tylerebowers/Luminator-Flipdot-Display/final board/80%complete.jpg

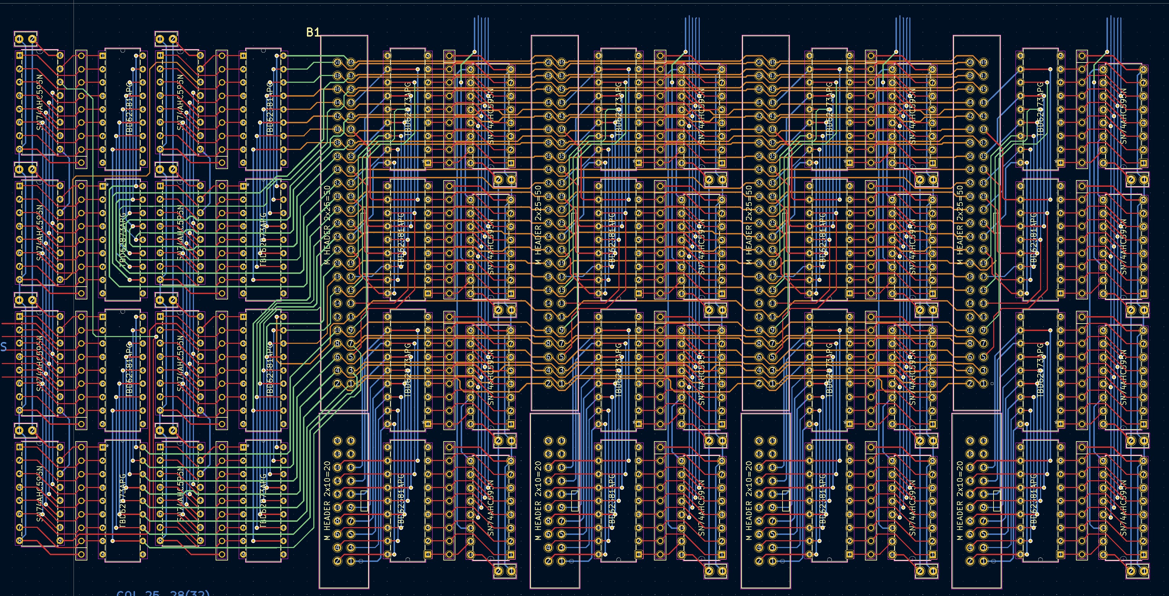
final board/80%complete.jpg
