tylerebowers/Luminator-Flipdot-Display/final board/90%complete.jpg

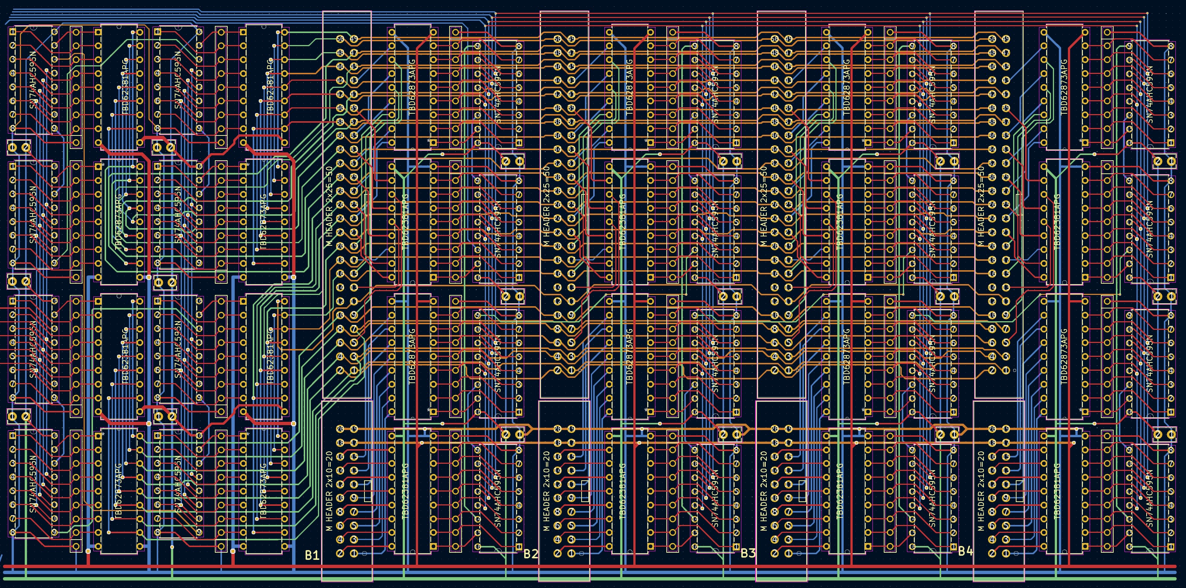
final board/90%complete.jpg
