tylerebowers/Luminator-Flipdot-Display/final board/100%Complete_3D.png

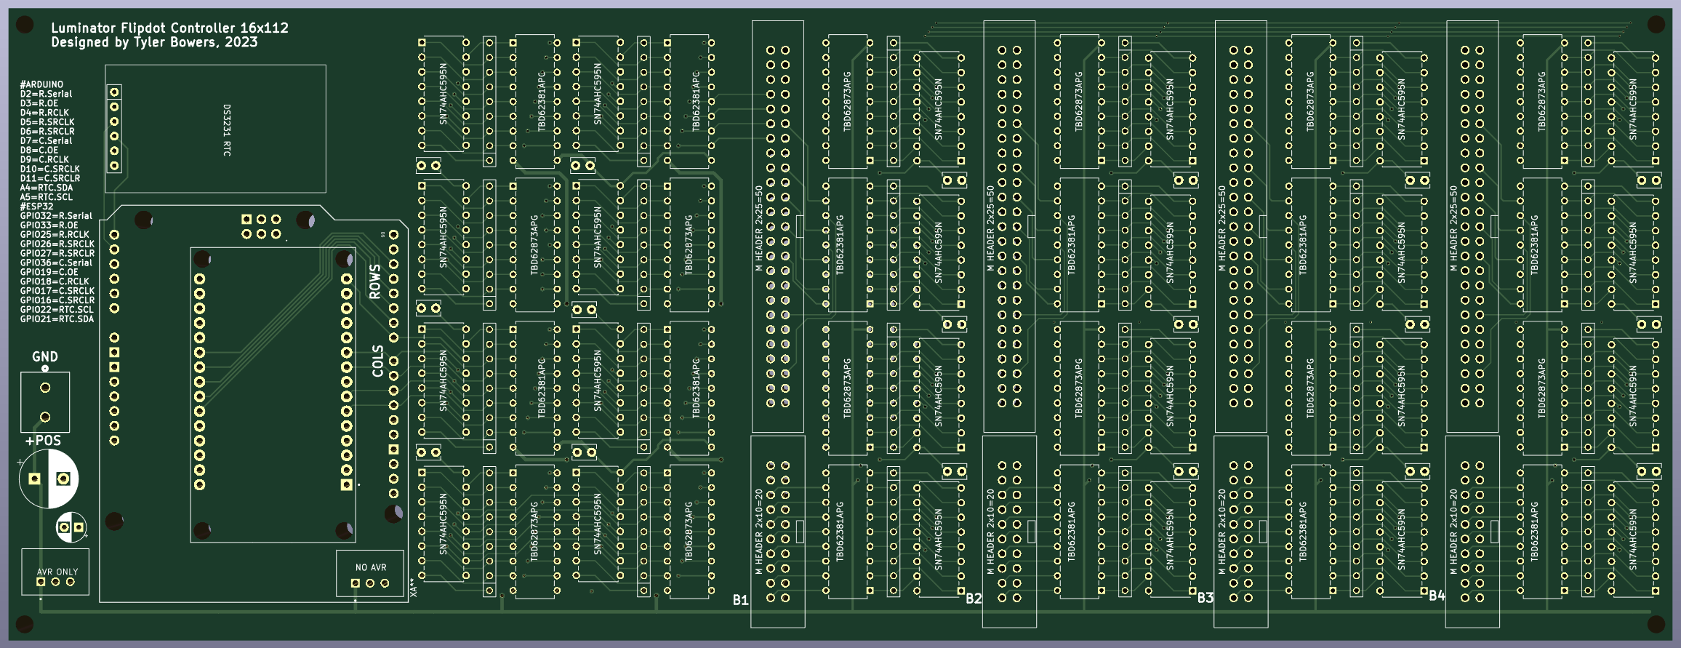
final board/100%Complete_3D.png
