tylerebowers/Luminator-Flipdot-Display/Other/board that doesn't work/Screenshot 2023-12-21 150835.png

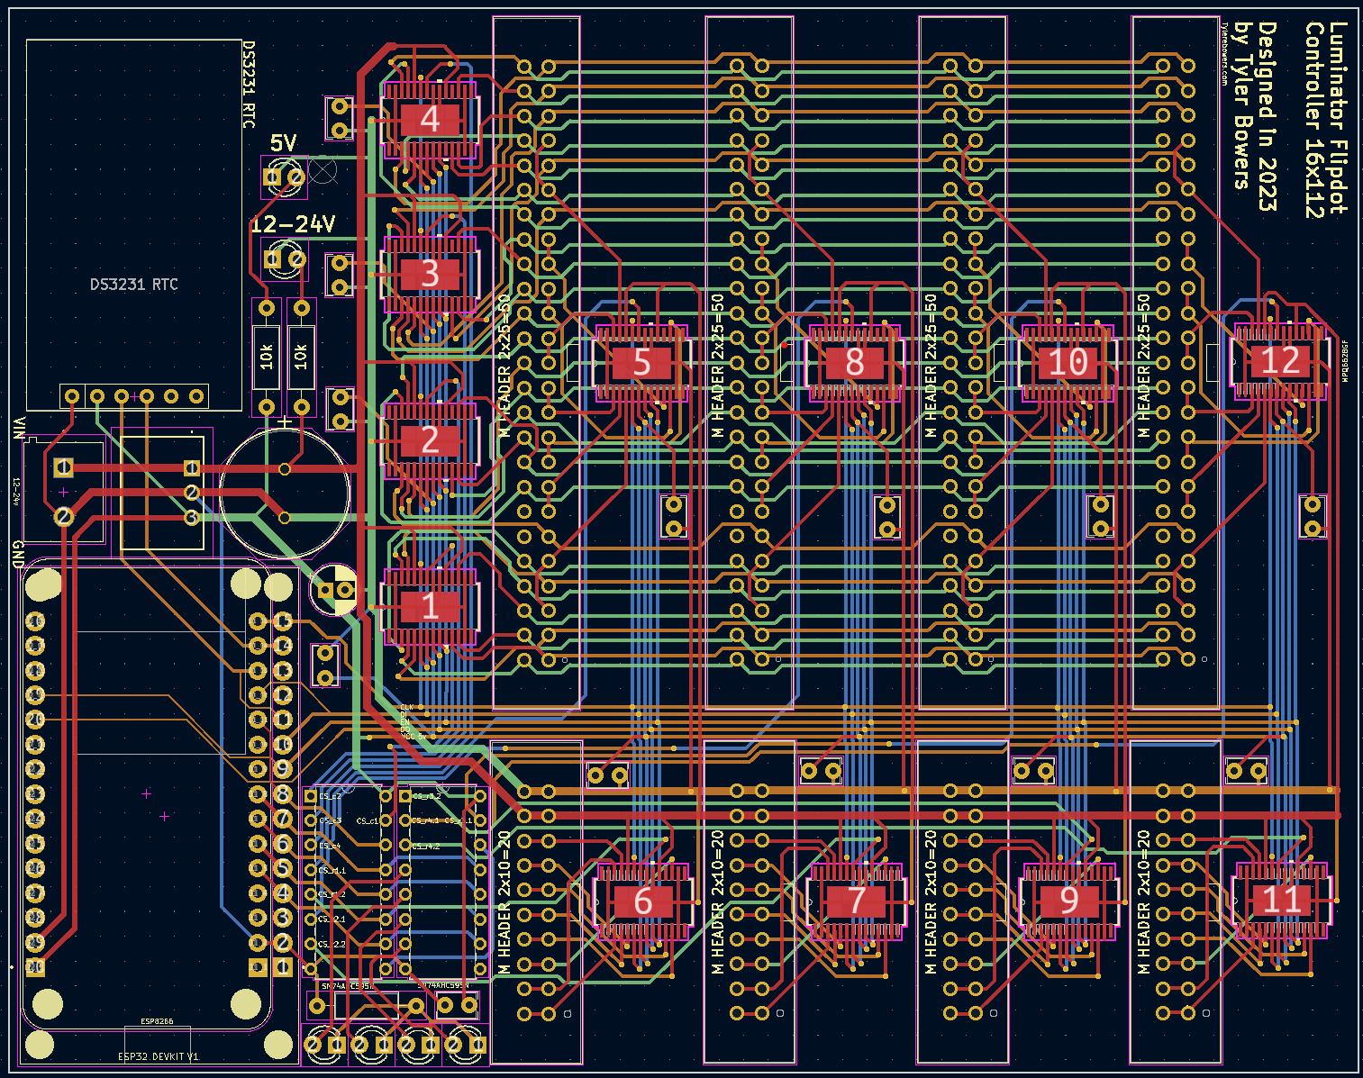
Other/board that doesn't work/Screenshot 2023-12-21 150835.png
