tylerebowers/Luminator-Flipdot-Display/Media/wiring.jpg

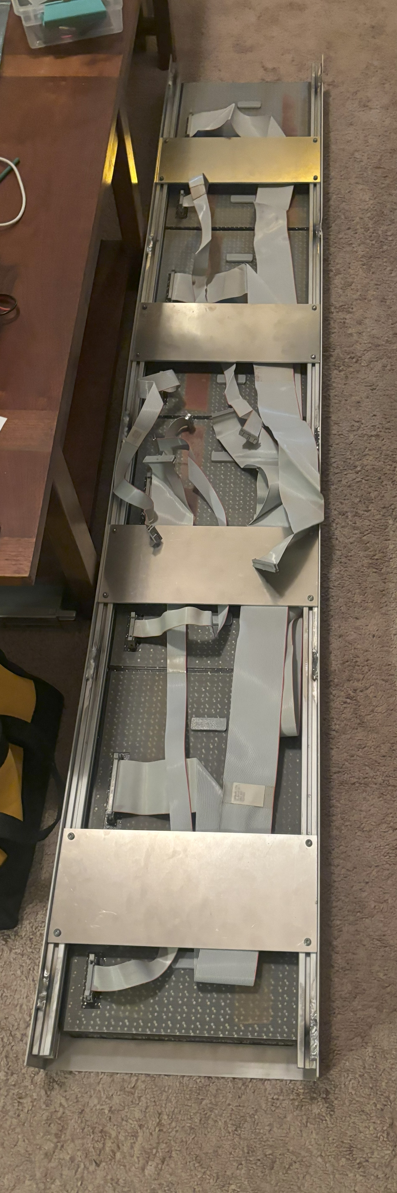
Media/wiring.jpg
