tylerebowers/Luminator-Flipdot-Display/Final Board/luminator.kicad_sch

## KiCad design Final Board/luminator.kicad_sch (2023-03-06)

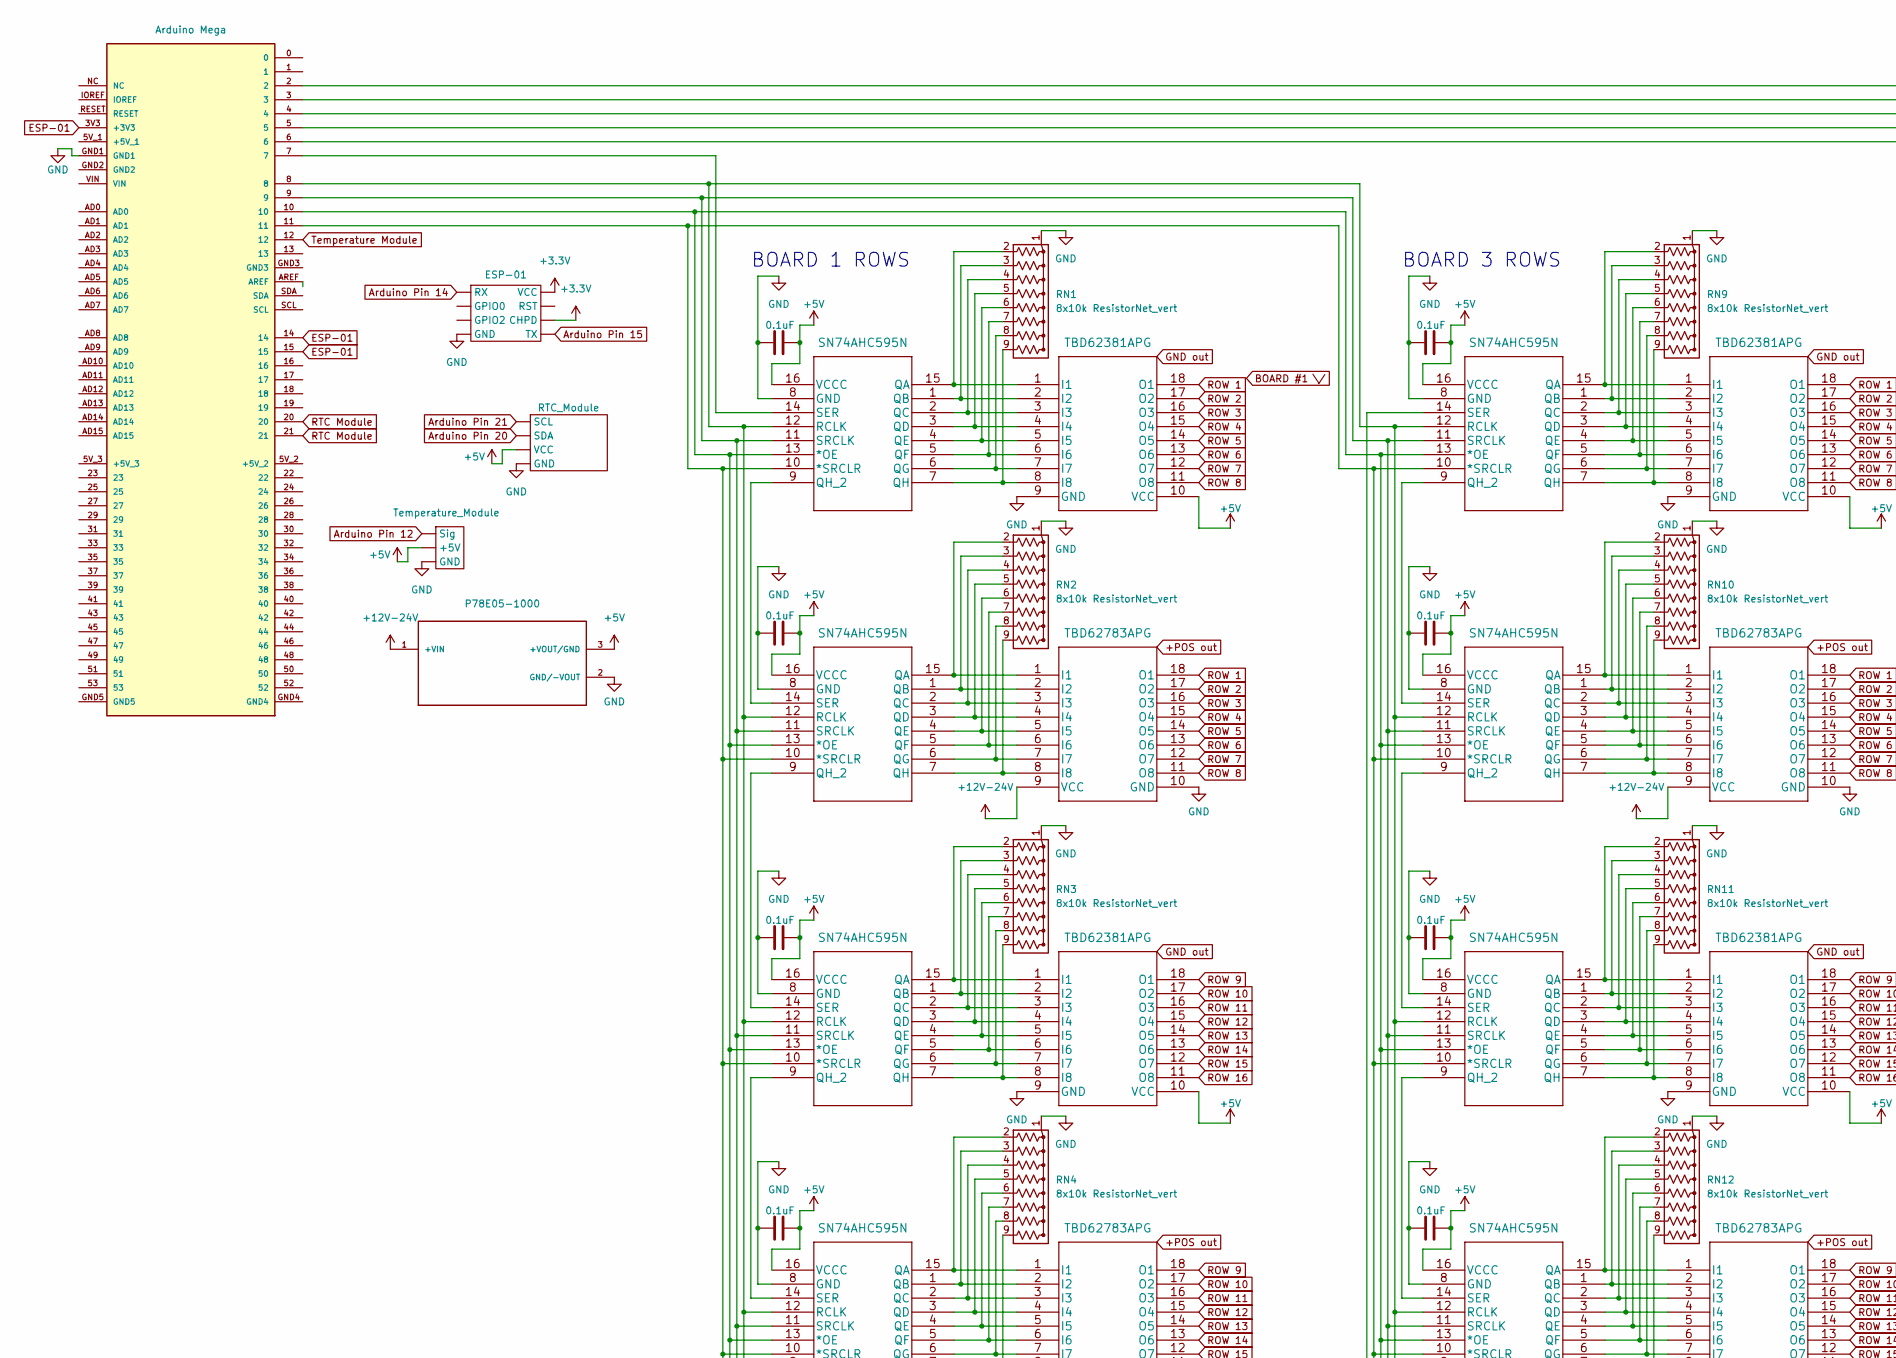
[picture p30: schematic luminator.kicad_sch, part in row 1, column 1]

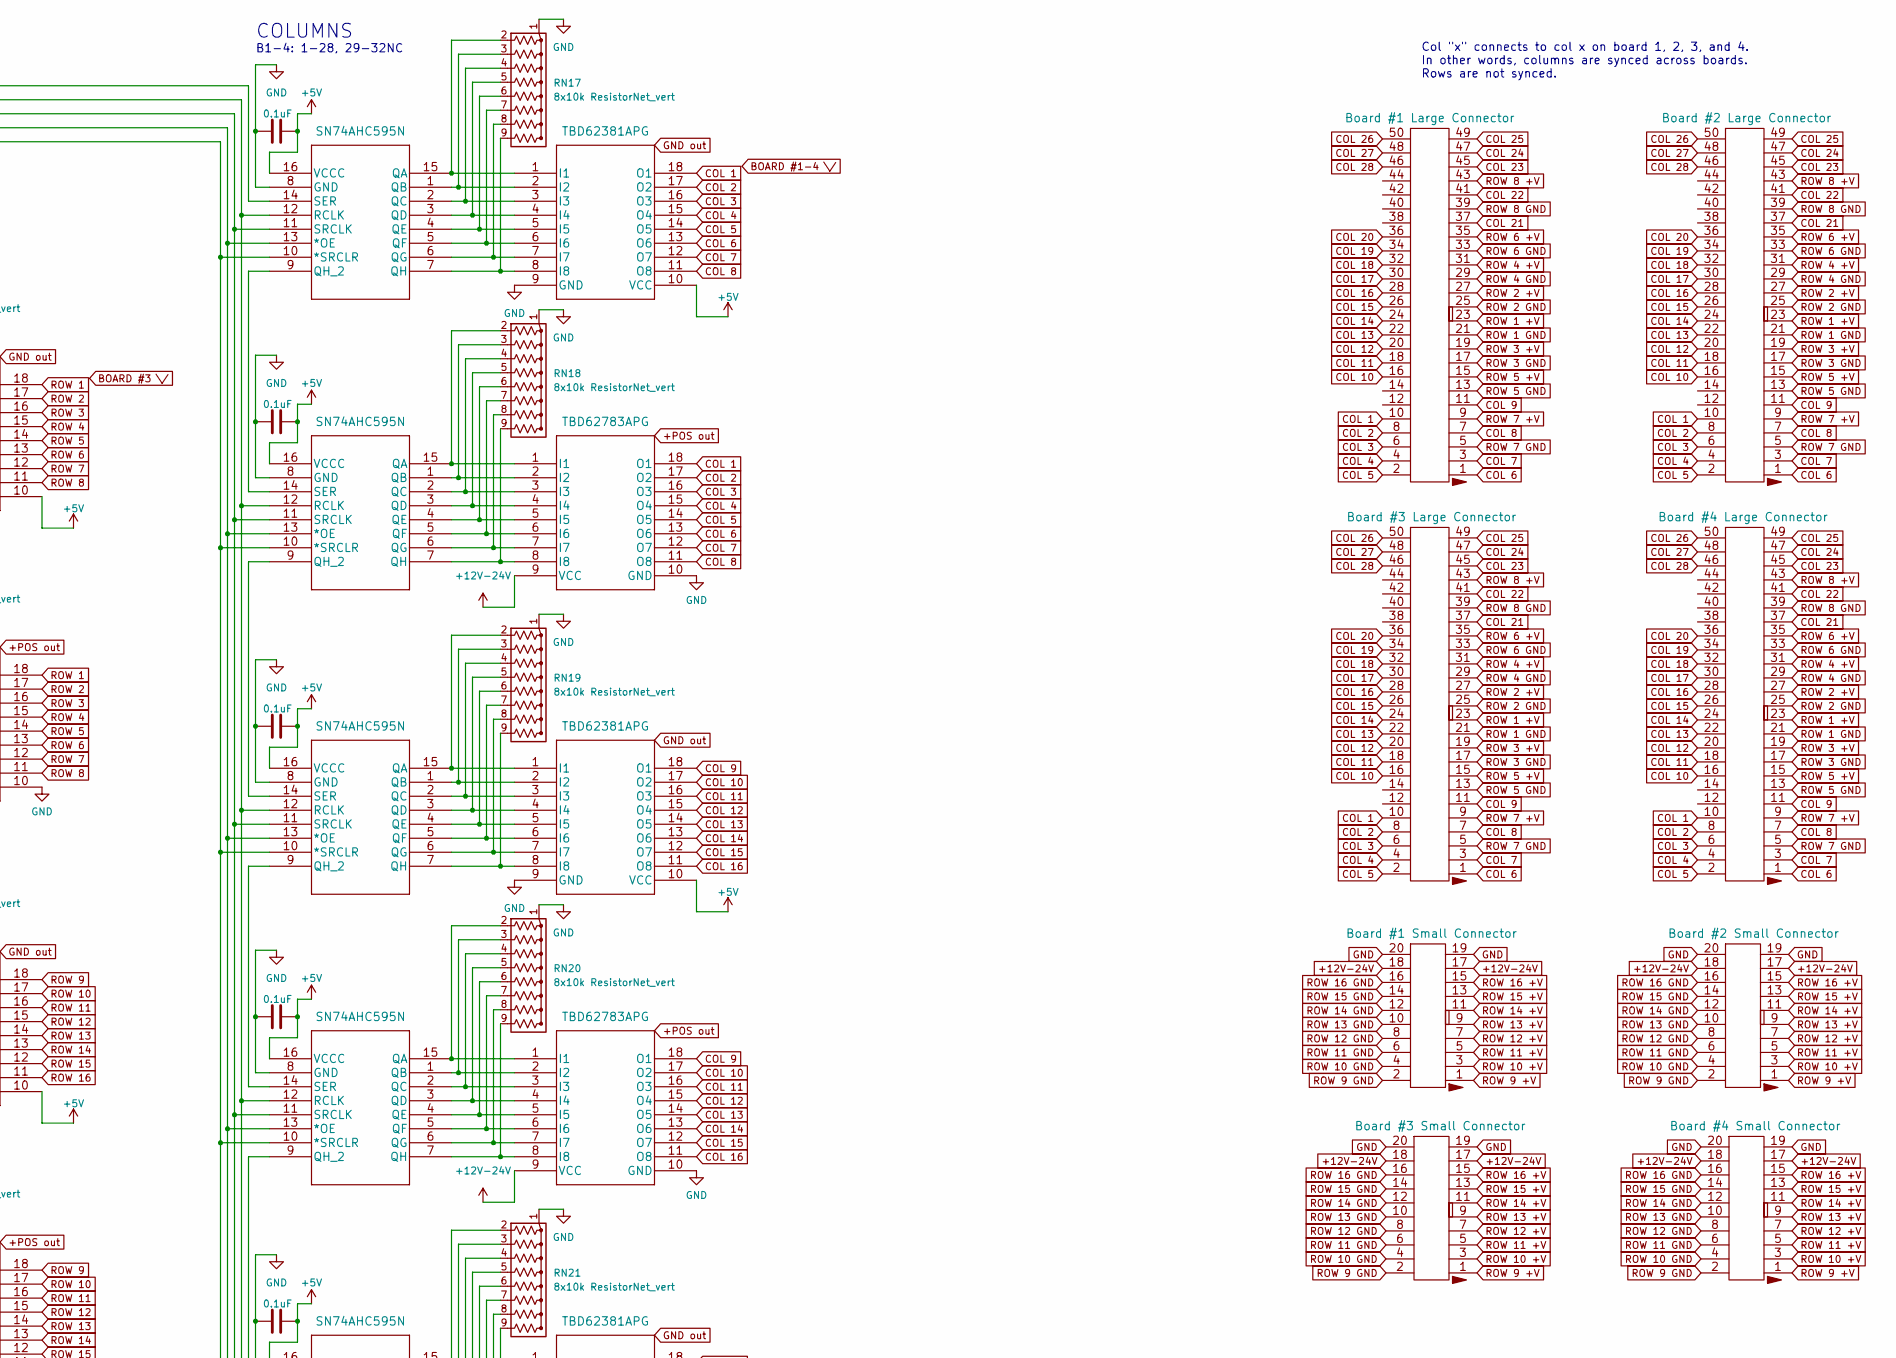
[picture p31: schematic luminator.kicad_sch, part in row 1, column 2]

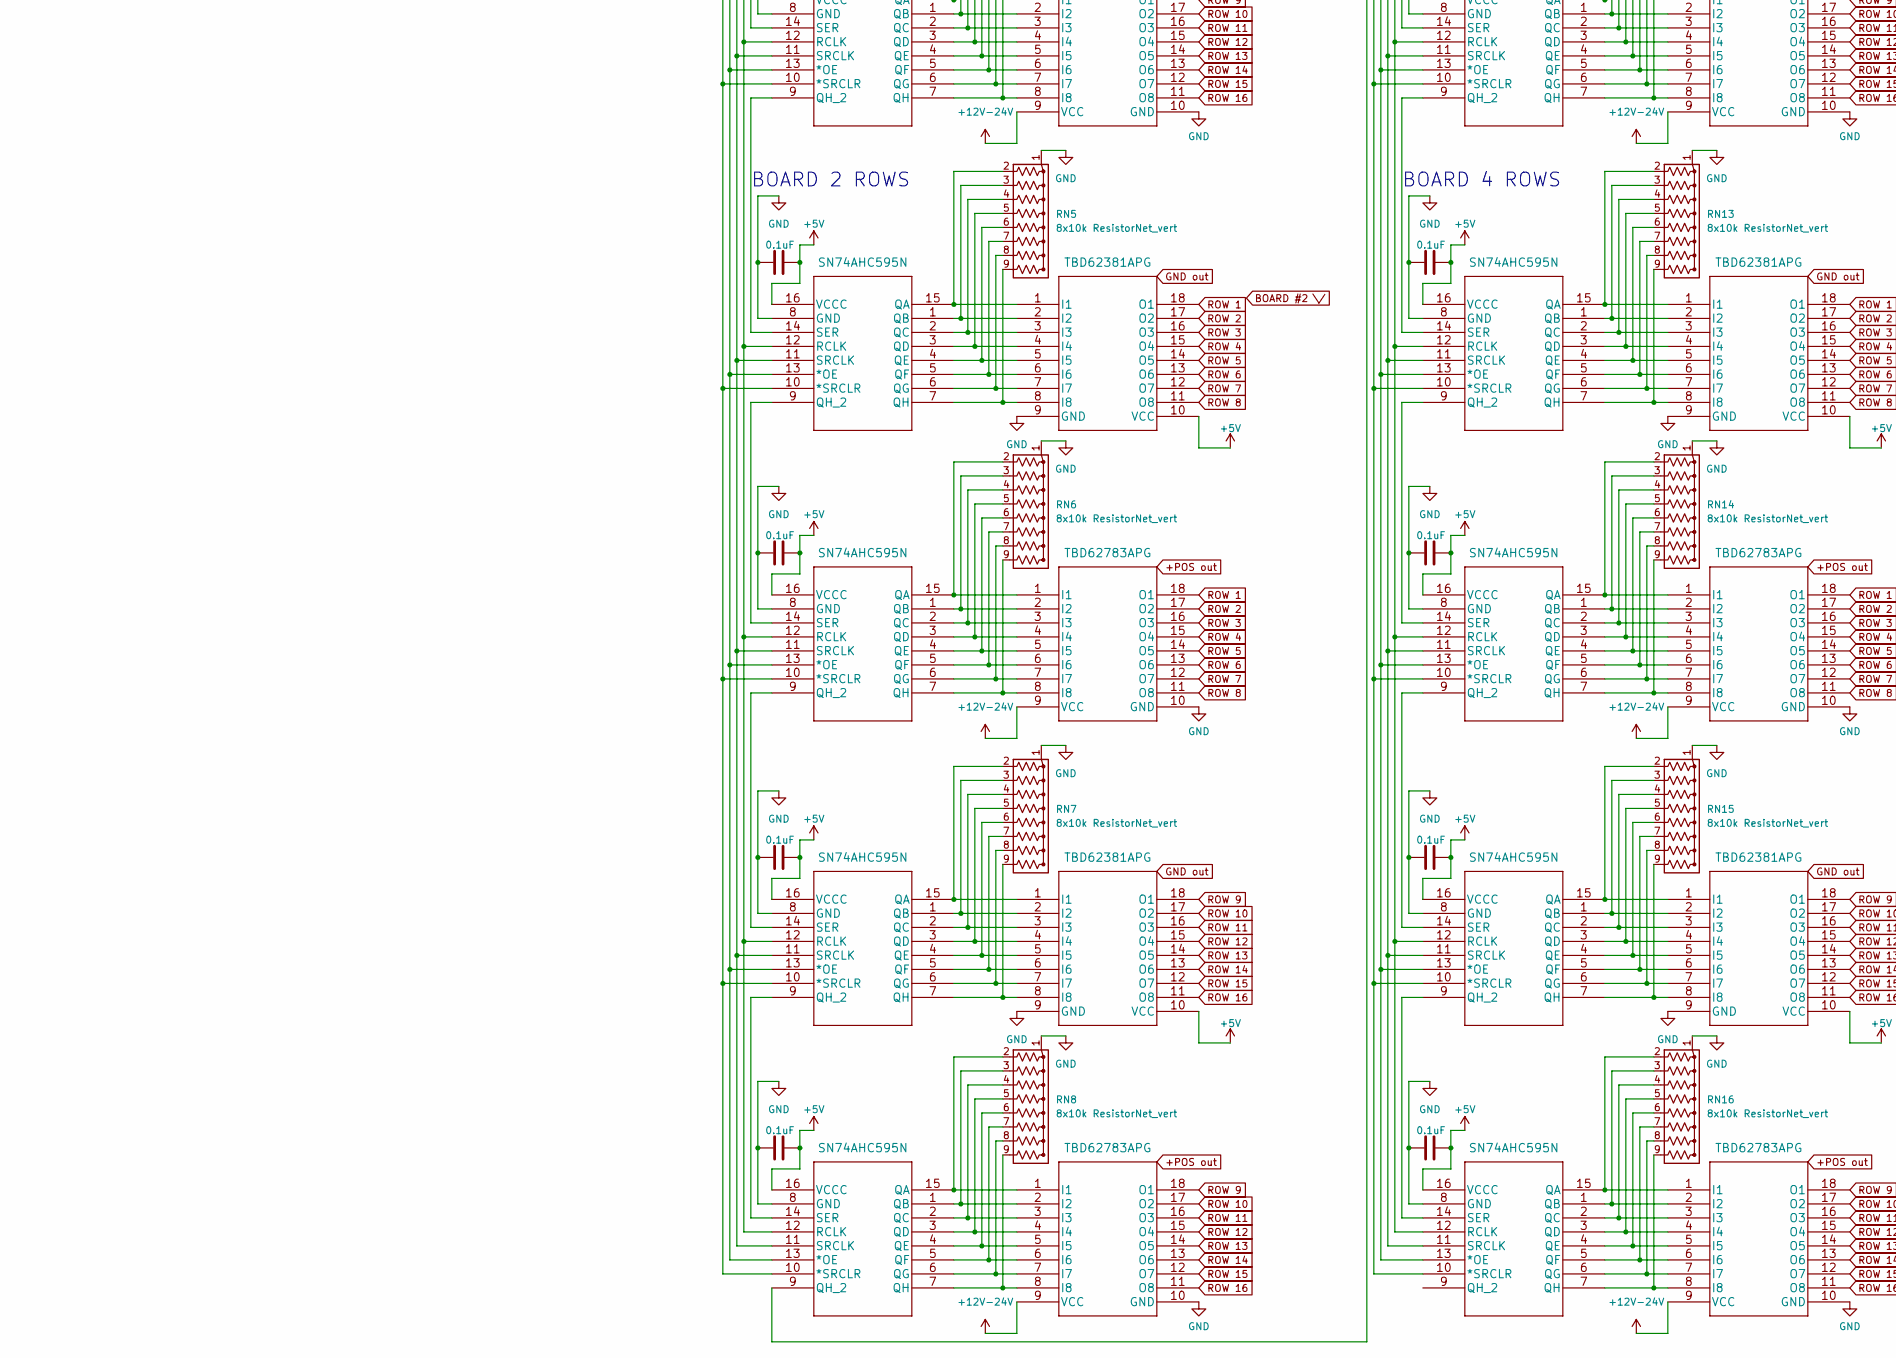
[picture p32: schematic luminator.kicad_sch, part in row 2, column 1]

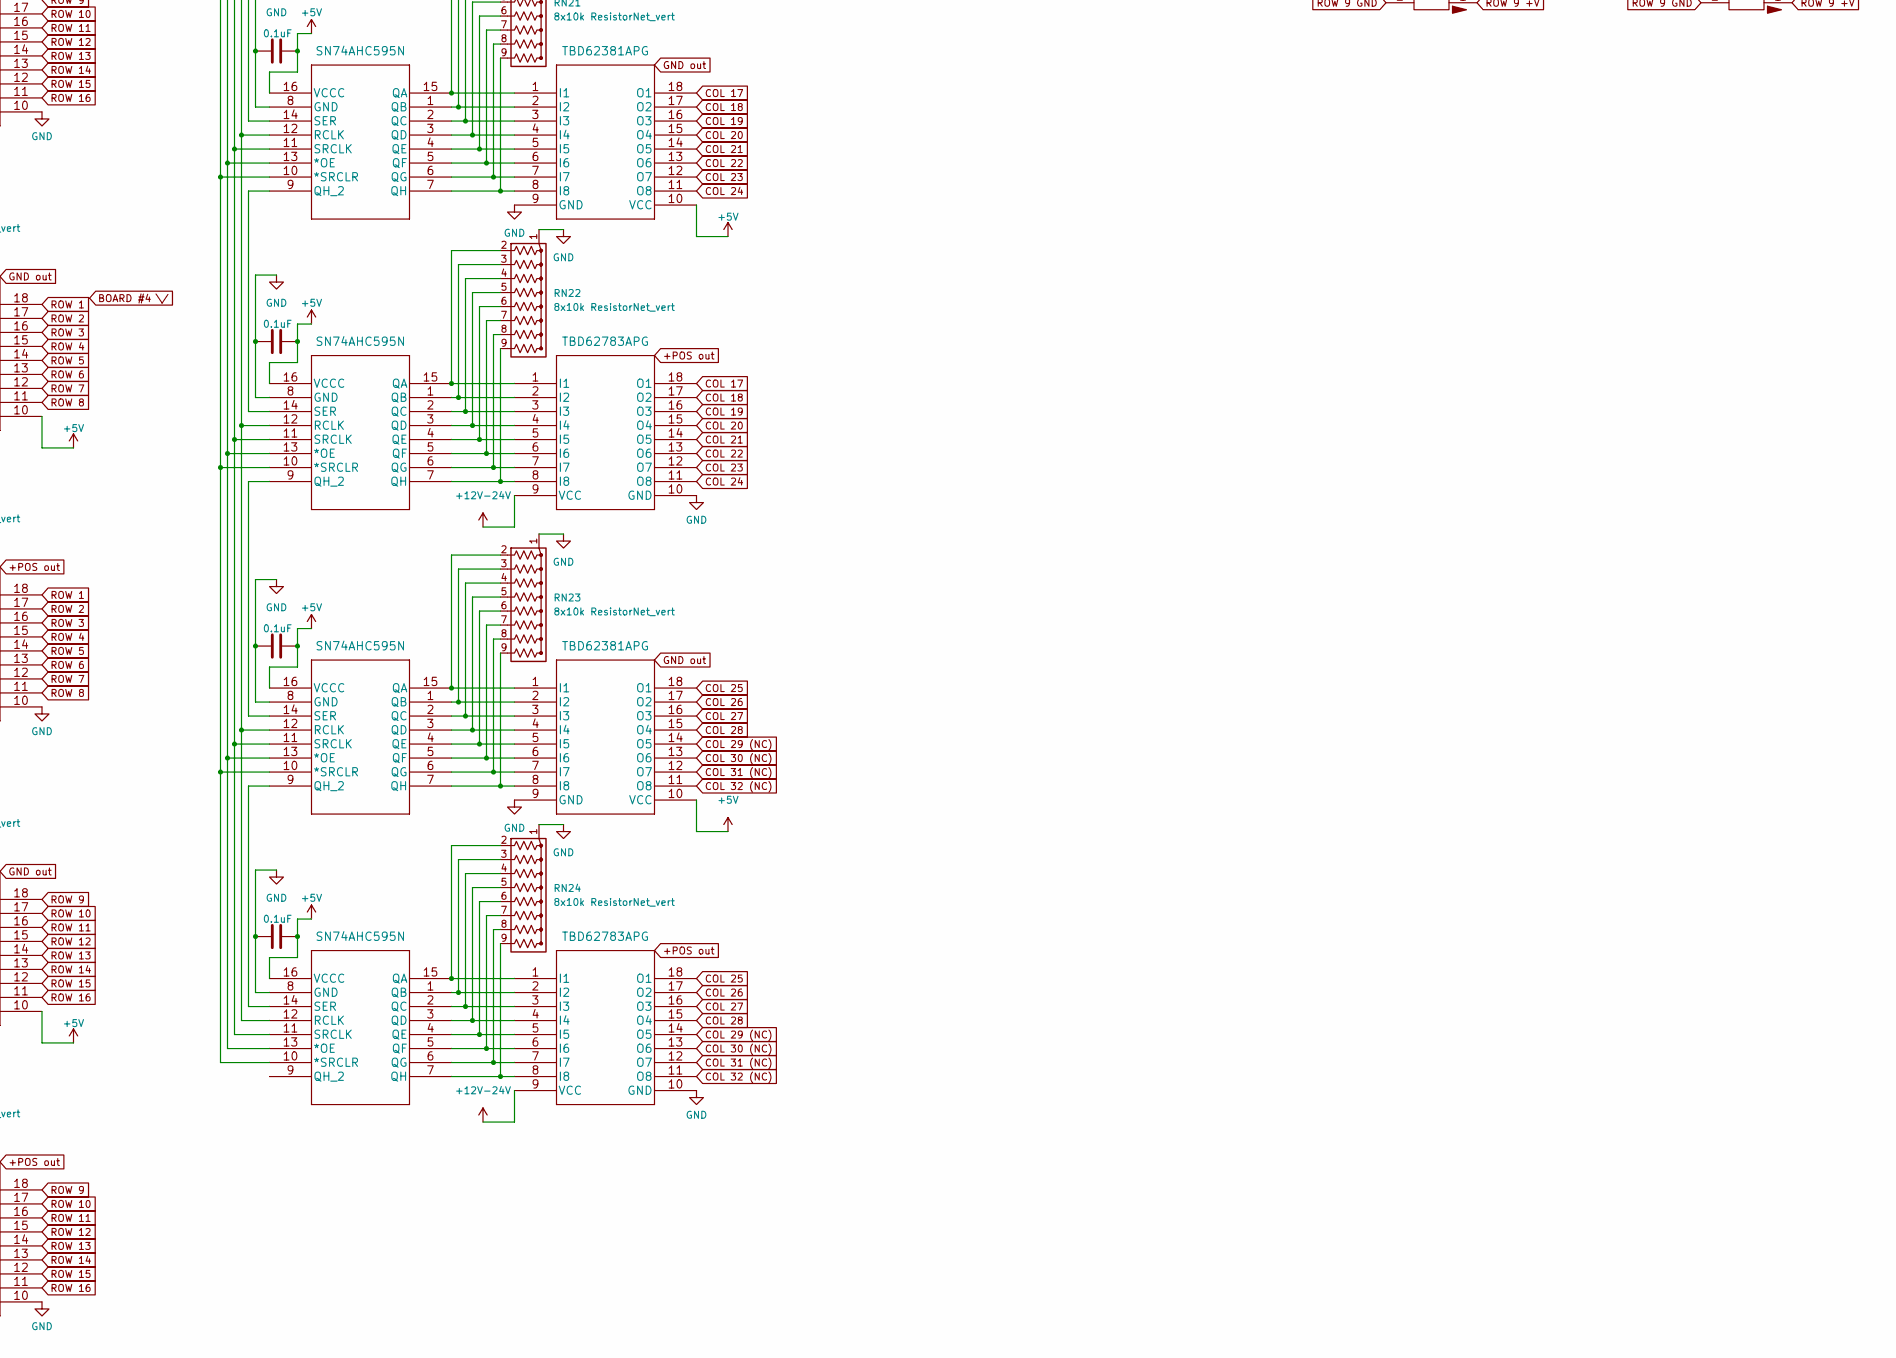
[picture p33: schematic luminator.kicad_sch, part in row 2, column 2]

Parts:
A1: Arduino Mega; ARDUINO_A000067
C1, C2, C3, C4, C5, C6, C7, C8, C9, C10, C11, C12, C13, C14, C15, C16, C17, C18, C19, C20, C21, C22, C23, C24: 0.1uF
J1: Board #1 Large Connector; CONN_SBH11-PBPC-D25-ST-BK_SUL
J2: Board #3 Large Connector; CONN_SBH11-PBPC-D25-ST-BK_SUL
J3: Board #1 Small Connector; CONN20_D10-ST-BK_SUL
J4: Board #3 Small Connector; CONN20_D10-ST-BK_SUL
J5: Board #2 Large Connector; CONN_SBH11-PBPC-D25-ST-BK_SUL
J6: Board #4 Large Connector; CONN_SBH11-PBPC-D25-ST-BK_SUL
J7: Board #2 Small Connector; CONN20_D10-ST-BK_SUL
J8: Board #4 Small Connector; CONN20_D10-ST-BK_SUL
PS1: P78E05-1000; CONV_P78E05-1000
RN1, RN2, RN3, RN4, RN5, RN6, RN7, RN8, RN9, RN10, RN11, RN12, RN13, RN14, RN15, RN16, RN17, RN18, RN19, RN20, RN21, RN22, RN23, RN24: 8x10k ResistorNet_vert; R_Array_SIP10
U1: Temperature_Module
U2: ESP-01
U3: RTC_Module
U4, U5, U6, U7, U8, U9, U10, U11, U20, U21, U22, U23, U24, U25, U26, U27, U36, U37, U38, U39, U40, U41, U42, U43: SN74AHC595N; N16
U12, U14, U16, U18, U28, U30, U32, U34, U44, U46, U48, U50: TBD62381APG; P-DIP18-300-2p54-001_TOS
U13, U15, U17, U19, U29, U31, U33, U35, U45, U47, U49, U51: TBD62783APG; P-DIP18-300-2p54-001_TOS

Connections:
+3.3V: U2.
+5V: C1.2, C2.2, C3.2, C4.2, C5.2, C6.2, C7.2, C8.2, C9.2, C10.2, C11.2, C12.2, C13.2, C14.2, C15.2, C16.2, C17.2, C18.2, C19.2, C20.2, C21.2, C22.2, C23.2, C24.2, PS1.3 (+VOUT/GND), U1., U3., U4.16 (VCCC), U5.16 (VCCC), U6.16 (VCCC), U7.16 (VCCC), U8.16 (VCCC), U9.16 (VCCC), U10.16 (VCCC), U11.16 (VCCC), U12.10 (VCC), U14.10 (VCC), U16.10 (VCC), U18.10 (VCC), U20.16 (VCCC), U21.16 (VCCC), U22.16 (VCCC), U23.16 (VCCC), U24.16 (VCCC), U25.16 (VCCC), U26.16 (VCCC), U27.16 (VCCC), U28.10 (VCC), U30.10 (VCC), U32.10 (VCC), U34.10 (VCC), U36.16 (VCCC), U37.16 (VCCC), U38.16 (VCCC), U39.16 (VCCC), U40.16 (VCCC), U41.16 (VCCC), U42.16 (VCCC), U43.16 (VCCC), U44.10 (VCC), U46.10 (VCC), U48.10 (VCC), U50.10 (VCC)
+12V-24V: J3.17, J3.18, J4.17, J4.18, J7.17, J7.18, J8.17, J8.18, PS1.1 (+VIN), U13.9 (VCC), U15.9 (VCC), U17.9 (VCC), U19.9 (VCC), U29.9 (VCC), U31.9 (VCC), U33.9 (VCC), U35.9 (VCC), U45.9 (VCC), U47.9 (VCC), U49.9 (VCC), U51.9 (VCC)
Arduino Pin 12: U1.
Arduino Pin 14: U2.
Arduino Pin 15: U2.
Arduino Pin 20: U3.
Arduino Pin 21: U3.
COL 1: J1.10, J2.10, J5.10, J6.10, U44.18 (O1), U45.18 (O1)
COL 2: J1.8, J2.8, J5.8, J6.8, U44.17 (O2), U45.17 (O2)
COL 3: J1.6, J2.6, J5.6, J6.6, U44.16 (O3), U45.16 (O3)
COL 4: J1.4, J2.4, J5.4, J6.4, U44.15 (O4), U45.15 (O4)
COL 5: J1.2, J2.2, J5.2, J6.2, U44.14 (O5), U45.14 (O5)
COL 6: J1.1, J2.1, J5.1, J6.1, U44.13 (O6), U45.13 (O6)
COL 7: J1.3, J2.3, J5.3, J6.3, U44.12 (O7), U45.12 (O7)
COL 8: J1.7, J2.7, J5.7, J6.7, U44.11 (O8), U45.11 (O8)
COL 9: J1.11, J2.11, J5.11, J6.11, U46.18 (O1), U47.18 (O1)
COL 10: J1.16, J2.16, J5.16, J6.16, U46.17 (O2), U47.17 (O2)
COL 11: J1.18, J2.18, J5.18, J6.18, U46.16 (O3), U47.16 (O3)
COL 12: J1.20, J2.20, J5.20, J6.20, U46.15 (O4), U47.15 (O4)
COL 13: J1.22, J2.22, J5.22, J6.22, U46.14 (O5), U47.14 (O5)
COL 14: J1.24, J2.24, J5.24, J6.24, U46.13 (O6), U47.13 (O6)
COL 15: J1.26, J2.26, J5.26, J6.26, U46.12 (O7), U47.12 (O7)
COL 16: J1.28, J2.28, J5.28, J6.28, U46.11 (O8), U47.11 (O8)
COL 17: J1.30, J2.30, J5.30, J6.30, U48.18 (O1), U49.18 (O1)
COL 18: J1.32, J2.32, J5.32, J6.32, U48.17 (O2), U49.17 (O2)
COL 19: J1.34, J2.34, J5.34, J6.34, U48.16 (O3), U49.16 (O3)
COL 20: J1.36, J2.36, J5.36, J6.36, U48.15 (O4), U49.15 (O4)
COL 21: J1.37, J2.37, J5.37, J6.37, U48.14 (O5), U49.14 (O5)
COL 22: J1.41, J2.41, J5.41, J6.41, U48.13 (O6), U49.13 (O6)
COL 23: J1.45, J2.45, J5.45, J6.45, U48.12 (O7), U49.12 (O7)
COL 24: J1.47, J2.47, J5.47, J6.47, U48.11 (O8), U49.11 (O8)
COL 25: J1.49, J2.49, J5.49, J6.49, U50.18 (O1), U51.18 (O1)
COL 26: J1.50, J2.50, J5.50, J6.50, U50.17 (O2), U51.17 (O2)
COL 27: J1.48, J2.48, J5.48, J6.48, U50.16 (O3), U51.16 (O3)
COL 28: J1.46, J2.46, J5.46, J6.46, U50.15 (O4), U51.15 (O4)
COL 29 (NC): U50.14 (O5), U51.14 (O5)
COL 30 (NC): U50.13 (O6), U51.13 (O6)
COL 31 (NC): U50.12 (O7), U51.12 (O7)
COL 32 (NC): U50.11 (O8), U51.11 (O8)
ESP-01: A1.3V3 (+3V3), A1.14, A1.15
GND: A1.GND1, C1.1, C2.1, C3.1, C4.1, C5.1, C6.1, C7.1, C8.1, C9.1, C10.1, C11.1, C12.1, C13.1, C14.1, C15.1, C16.1, C17.1, C18.1, C19.1, C20.1, C21.1, C22.1, C23.1, C24.1, J3.19, J3.20, J4.19, J4.20, J7.19, J7.20, J8.19, J8.20, PS1.2 (GND/-VOUT), RN1.1 (common), RN2.1 (common), RN3.1 (common), RN4.1 (common), RN5.1 (common), RN6.1 (common), RN7.1 (common), RN8.1 (common), RN9.1 (common), RN10.1 (common), RN11.1 (common), RN12.1 (common), RN13.1 (common), RN14.1 (common), RN15.1 (common), RN16.1 (common), RN17.1 (common), RN18.1 (common), RN19.1 (common), RN20.1 (common), RN21.1 (common), RN22.1 (common), RN23.1 (common), RN24.1 (common), U1., U2., U3., U4.8 (GND), U5.8 (GND), U6.8 (GND), U7.8 (GND), U8.8 (GND), U9.8 (GND), U10.8 (GND), U11.8 (GND), U12.9 (GND), U13.10 (GND), U14.9 (GND), U15.10 (GND), U16.9 (GND), U17.10 (GND), U18.9 (GND), U19.10 (GND), U20.8 (GND), U21.8 (GND), U22.8 (GND), U23.8 (GND), U24.8 (GND), U25.8 (GND), U26.8 (GND), U27.8 (GND), U28.9 (GND), U29.10 (GND), U30.9 (GND), U31.10 (GND), U32.9 (GND), U33.10 (GND), U34.9 (GND), U35.10 (GND), U36.8 (GND), U37.8 (GND), U38.8 (GND), U39.8 (GND), U40.8 (GND), U41.8 (GND), U42.8 (GND), U43.8 (GND), U44.9 (GND), U45.10 (GND), U46.9 (GND), U47.10 (GND), U48.9 (GND), U49.10 (GND), U50.9 (GND), U51.10 (GND)
unnamed: A1.2, U36.14 (SER)
unnamed: A1.3, U36.12 (RCLK), U37.12 (RCLK), U38.12 (RCLK), U39.12 (RCLK), U40.12 (RCLK), U41.12 (RCLK), U42.12 (RCLK), U43.12 (RCLK)
unnamed: A1.4, U36.11 (SRCLK), U37.11 (SRCLK), U38.11 (SRCLK), U39.11 (SRCLK), U40.11 (SRCLK), U41.11 (SRCLK), U42.11 (SRCLK), U43.11 (SRCLK)
unnamed: A1.5, U36.13 (*OE), U37.13 (*OE), U38.13 (*OE), U39.13 (*OE), U40.13 (*OE), U41.13 (*OE), U42.13 (*OE), U43.13 (*OE)
unnamed: A1.6, U36.10 (*SRCLR), U37.10 (*SRCLR), U38.10 (*SRCLR), U39.10 (*SRCLR), U40.10 (*SRCLR), U41.10 (*SRCLR), U42.10 (*SRCLR), U43.10 (*SRCLR)
unnamed: A1.7, U4.14 (SER)
unnamed: A1.8, U4.12 (RCLK), U5.12 (RCLK), U6.12 (RCLK), U7.12 (RCLK), U8.12 (RCLK), U9.12 (RCLK), U10.12 (RCLK), U11.12 (RCLK), U20.12 (RCLK), U21.12 (RCLK), U22.12 (RCLK), U23.12 (RCLK), U24.12 (RCLK), U25.12 (RCLK), U26.12 (RCLK), U27.12 (RCLK)
unnamed: A1.9, U4.11 (SRCLK), U5.11 (SRCLK), U6.11 (SRCLK), U7.11 (SRCLK), U8.11 (SRCLK), U9.11 (SRCLK), U10.11 (SRCLK), U11.11 (SRCLK), U20.11 (SRCLK), U21.11 (SRCLK), U22.11 (SRCLK), U23.11 (SRCLK), U24.11 (SRCLK), U25.11 (SRCLK), U26.11 (SRCLK), U27.11 (SRCLK)
unnamed: A1.10, U4.13 (*OE), U5.13 (*OE), U6.13 (*OE), U7.13 (*OE), U8.13 (*OE), U9.13 (*OE), U10.13 (*OE), U11.13 (*OE), U20.13 (*OE), U21.13 (*OE), U22.13 (*OE), U23.13 (*OE), U24.13 (*OE), U25.13 (*OE), U26.13 (*OE), U27.13 (*OE)
unnamed: A1.11, U4.10 (*SRCLR), U5.10 (*SRCLR), U6.10 (*SRCLR), U7.10 (*SRCLR), U8.10 (*SRCLR), U9.10 (*SRCLR), U10.10 (*SRCLR), U11.10 (*SRCLR), U20.10 (*SRCLR), U21.10 (*SRCLR), U22.10 (*SRCLR), U23.10 (*SRCLR), U24.10 (*SRCLR), U25.10 (*SRCLR), U26.10 (*SRCLR), U27.10 (*SRCLR)
unnamed: RN1.2 (R1), U4.15 (QA), U12.1 (I1)
unnamed: RN1.3 (R2), U4.1 (QB), U12.2 (I2)
unnamed: RN1.4 (R3), U4.2 (QC), U12.3 (I3)
unnamed: RN1.5 (R4), U4.3 (QD), U12.4 (I4)
unnamed: RN1.6 (R5), U4.4 (QE), U12.5 (I5)
unnamed: RN1.7 (R6), U4.5 (QF), U12.6 (I6)
unnamed: RN1.8 (R7), U4.6 (QG), U12.7 (I7)
unnamed: RN1.9 (R8), U4.7 (QH), U12.8 (I8)
unnamed: RN2.2 (R1), U5.15 (QA), U13.1 (I1)
unnamed: RN2.3 (R2), U5.1 (QB), U13.2 (I2)
unnamed: RN2.4 (R3), U5.2 (QC), U13.3 (I3)
unnamed: RN2.5 (R4), U5.3 (QD), U13.4 (I4)
unnamed: RN2.6 (R5), U5.4 (QE), U13.5 (I5)
unnamed: RN2.7 (R6), U5.5 (QF), U13.6 (I6)
unnamed: RN2.8 (R7), U5.6 (QG), U13.7 (I7)
unnamed: RN2.9 (R8), U5.7 (QH), U13.8 (I8)
unnamed: RN3.2 (R1), U6.15 (QA), U14.1 (I1)
unnamed: RN3.3 (R2), U6.1 (QB), U14.2 (I2)
unnamed: RN3.4 (R3), U6.2 (QC), U14.3 (I3)
unnamed: RN3.5 (R4), U6.3 (QD), U14.4 (I4)
unnamed: RN3.6 (R5), U6.4 (QE), U14.5 (I5)
unnamed: RN3.7 (R6), U6.5 (QF), U14.6 (I6)
unnamed: RN3.8 (R7), U6.6 (QG), U14.7 (I7)
unnamed: RN3.9 (R8), U6.7 (QH), U14.8 (I8)
unnamed: RN4.2 (R1), U7.15 (QA), U15.1 (I1)
unnamed: RN4.3 (R2), U7.1 (QB), U15.2 (I2)
unnamed: RN4.4 (R3), U7.2 (QC), U15.3 (I3)
unnamed: RN4.5 (R4), U7.3 (QD), U15.4 (I4)
unnamed: RN4.6 (R5), U7.4 (QE), U15.5 (I5)
unnamed: RN4.7 (R6), U7.5 (QF), U15.6 (I6)
unnamed: RN4.8 (R7), U7.6 (QG), U15.7 (I7)
unnamed: RN4.9 (R8), U7.7 (QH), U15.8 (I8)
unnamed: RN5.2 (R1), U8.15 (QA), U16.1 (I1)
unnamed: RN5.3 (R2), U8.1 (QB), U16.2 (I2)
unnamed: RN5.4 (R3), U8.2 (QC), U16.3 (I3)
unnamed: RN5.5 (R4), U8.3 (QD), U16.4 (I4)
unnamed: RN5.6 (R5), U8.4 (QE), U16.5 (I5)
unnamed: RN5.7 (R6), U8.5 (QF), U16.6 (I6)
unnamed: RN5.8 (R7), U8.6 (QG), U16.7 (I7)
unnamed: RN5.9 (R8), U8.7 (QH), U16.8 (I8)
unnamed: RN6.2 (R1), U9.15 (QA), U17.1 (I1)
unnamed: RN6.3 (R2), U9.1 (QB), U17.2 (I2)
unnamed: RN6.4 (R3), U9.2 (QC), U17.3 (I3)
unnamed: RN6.5 (R4), U9.3 (QD), U17.4 (I4)
unnamed: RN6.6 (R5), U9.4 (QE), U17.5 (I5)
unnamed: RN6.7 (R6), U9.5 (QF), U17.6 (I6)
unnamed: RN6.8 (R7), U9.6 (QG), U17.7 (I7)
unnamed: RN6.9 (R8), U9.7 (QH), U17.8 (I8)
unnamed: RN7.2 (R1), U10.15 (QA), U18.1 (I1)
unnamed: RN7.3 (R2), U10.1 (QB), U18.2 (I2)
unnamed: RN7.4 (R3), U10.2 (QC), U18.3 (I3)
unnamed: RN7.5 (R4), U10.3 (QD), U18.4 (I4)
unnamed: RN7.6 (R5), U10.4 (QE), U18.5 (I5)
unnamed: RN7.7 (R6), U10.5 (QF), U18.6 (I6)
unnamed: RN7.8 (R7), U10.6 (QG), U18.7 (I7)
unnamed: RN7.9 (R8), U10.7 (QH), U18.8 (I8)
unnamed: RN8.2 (R1), U11.15 (QA), U19.1 (I1)
unnamed: RN8.3 (R2), U11.1 (QB), U19.2 (I2)
unnamed: RN8.4 (R3), U11.2 (QC), U19.3 (I3)
unnamed: RN8.5 (R4), U11.3 (QD), U19.4 (I4)
unnamed: RN8.6 (R5), U11.4 (QE), U19.5 (I5)
unnamed: RN8.7 (R6), U11.5 (QF), U19.6 (I6)
unnamed: RN8.8 (R7), U11.6 (QG), U19.7 (I7)
unnamed: RN8.9 (R8), U11.7 (QH), U19.8 (I8)
unnamed: RN9.2 (R1), U20.15 (QA), U28.1 (I1)
unnamed: RN9.3 (R2), U20.1 (QB), U28.2 (I2)
unnamed: RN9.4 (R3), U20.2 (QC), U28.3 (I3)
unnamed: RN9.5 (R4), U20.3 (QD), U28.4 (I4)
unnamed: RN9.6 (R5), U20.4 (QE), U28.5 (I5)
unnamed: RN9.7 (R6), U20.5 (QF), U28.6 (I6)
unnamed: RN9.8 (R7), U20.6 (QG), U28.7 (I7)
unnamed: RN9.9 (R8), U20.7 (QH), U28.8 (I8)
unnamed: RN10.2 (R1), U21.15 (QA), U29.1 (I1)
unnamed: RN10.3 (R2), U21.1 (QB), U29.2 (I2)
unnamed: RN10.4 (R3), U21.2 (QC), U29.3 (I3)
unnamed: RN10.5 (R4), U21.3 (QD), U29.4 (I4)
unnamed: RN10.6 (R5), U21.4 (QE), U29.5 (I5)
unnamed: RN10.7 (R6), U21.5 (QF), U29.6 (I6)
unnamed: RN10.8 (R7), U21.6 (QG), U29.7 (I7)
unnamed: RN10.9 (R8), U21.7 (QH), U29.8 (I8)
unnamed: RN11.2 (R1), U22.15 (QA), U30.1 (I1)
unnamed: RN11.3 (R2), U22.1 (QB), U30.2 (I2)
unnamed: RN11.4 (R3), U22.2 (QC), U30.3 (I3)
unnamed: RN11.5 (R4), U22.3 (QD), U30.4 (I4)
unnamed: RN11.6 (R5), U22.4 (QE), U30.5 (I5)
unnamed: RN11.7 (R6), U22.5 (QF), U30.6 (I6)
unnamed: RN11.8 (R7), U22.6 (QG), U30.7 (I7)
unnamed: RN11.9 (R8), U22.7 (QH), U30.8 (I8)
unnamed: RN12.2 (R1), U23.15 (QA), U31.1 (I1)
unnamed: RN12.3 (R2), U23.1 (QB), U31.2 (I2)
unnamed: RN12.4 (R3), U23.2 (QC), U31.3 (I3)
unnamed: RN12.5 (R4), U23.3 (QD), U31.4 (I4)
unnamed: RN12.6 (R5), U23.4 (QE), U31.5 (I5)
unnamed: RN12.7 (R6), U23.5 (QF), U31.6 (I6)
unnamed: RN12.8 (R7), U23.6 (QG), U31.7 (I7)
unnamed: RN12.9 (R8), U23.7 (QH), U31.8 (I8)
unnamed: RN13.2 (R1), U24.15 (QA), U32.1 (I1)
unnamed: RN13.3 (R2), U24.1 (QB), U32.2 (I2)
unnamed: RN13.4 (R3), U24.2 (QC), U32.3 (I3)
unnamed: RN13.5 (R4), U24.3 (QD), U32.4 (I4)
unnamed: RN13.6 (R5), U24.4 (QE), U32.5 (I5)
unnamed: RN13.7 (R6), U24.5 (QF), U32.6 (I6)
unnamed: RN13.8 (R7), U24.6 (QG), U32.7 (I7)
unnamed: RN13.9 (R8), U24.7 (QH), U32.8 (I8)
unnamed: RN14.2 (R1), U25.15 (QA), U33.1 (I1)
unnamed: RN14.3 (R2), U25.1 (QB), U33.2 (I2)
unnamed: RN14.4 (R3), U25.2 (QC), U33.3 (I3)
unnamed: RN14.5 (R4), U25.3 (QD), U33.4 (I4)
unnamed: RN14.6 (R5), U25.4 (QE), U33.5 (I5)
unnamed: RN14.7 (R6), U25.5 (QF), U33.6 (I6)
unnamed: RN14.8 (R7), U25.6 (QG), U33.7 (I7)
unnamed: RN14.9 (R8), U25.7 (QH), U33.8 (I8)
unnamed: RN15.2 (R1), U26.15 (QA), U34.1 (I1)
unnamed: RN15.3 (R2), U26.1 (QB), U34.2 (I2)
unnamed: RN15.4 (R3), U26.2 (QC), U34.3 (I3)
unnamed: RN15.5 (R4), U26.3 (QD), U34.4 (I4)
unnamed: RN15.6 (R5), U26.4 (QE), U34.5 (I5)
unnamed: RN15.7 (R6), U26.5 (QF), U34.6 (I6)
unnamed: RN15.8 (R7), U26.6 (QG), U34.7 (I7)
unnamed: RN15.9 (R8), U26.7 (QH), U34.8 (I8)
unnamed: RN16.2 (R1), U27.15 (QA), U35.1 (I1)
unnamed: RN16.3 (R2), U27.1 (QB), U35.2 (I2)
unnamed: RN16.4 (R3), U27.2 (QC), U35.3 (I3)
unnamed: RN16.5 (R4), U27.3 (QD), U35.4 (I4)
unnamed: RN16.6 (R5), U27.4 (QE), U35.5 (I5)
unnamed: RN16.7 (R6), U27.5 (QF), U35.6 (I6)
unnamed: RN16.8 (R7), U27.6 (QG), U35.7 (I7)
unnamed: RN16.9 (R8), U27.7 (QH), U35.8 (I8)
unnamed: RN17.2 (R1), U36.15 (QA), U44.1 (I1)
unnamed: RN17.3 (R2), U36.1 (QB), U44.2 (I2)
unnamed: RN17.4 (R3), U36.2 (QC), U44.3 (I3)
unnamed: RN17.5 (R4), U36.3 (QD), U44.4 (I4)
unnamed: RN17.6 (R5), U36.4 (QE), U44.5 (I5)
unnamed: RN17.7 (R6), U36.5 (QF), U44.6 (I6)
unnamed: RN17.8 (R7), U36.6 (QG), U44.7 (I7)
unnamed: RN17.9 (R8), U36.7 (QH), U44.8 (I8)
unnamed: RN18.2 (R1), U37.15 (QA), U45.1 (I1)
unnamed: RN18.3 (R2), U37.1 (QB), U45.2 (I2)
unnamed: RN18.4 (R3), U37.2 (QC), U45.3 (I3)
unnamed: RN18.5 (R4), U37.3 (QD), U45.4 (I4)
unnamed: RN18.6 (R5), U37.4 (QE), U45.5 (I5)
unnamed: RN18.7 (R6), U37.5 (QF), U45.6 (I6)
unnamed: RN18.8 (R7), U37.6 (QG), U45.7 (I7)
unnamed: RN18.9 (R8), U37.7 (QH), U45.8 (I8)
unnamed: RN19.2 (R1), U38.15 (QA), U46.1 (I1)
unnamed: RN19.3 (R2), U38.1 (QB), U46.2 (I2)
unnamed: RN19.4 (R3), U38.2 (QC), U46.3 (I3)
unnamed: RN19.5 (R4), U38.3 (QD), U46.4 (I4)
unnamed: RN19.6 (R5), U38.4 (QE), U46.5 (I5)
unnamed: RN19.7 (R6), U38.5 (QF), U46.6 (I6)
unnamed: RN19.8 (R7), U38.6 (QG), U46.7 (I7)
unnamed: RN19.9 (R8), U38.7 (QH), U46.8 (I8)
unnamed: RN20.2 (R1), U39.15 (QA), U47.1 (I1)
unnamed: RN20.3 (R2), U39.1 (QB), U47.2 (I2)
unnamed: RN20.4 (R3), U39.2 (QC), U47.3 (I3)
unnamed: RN20.5 (R4), U39.3 (QD), U47.4 (I4)
unnamed: RN20.6 (R5), U39.4 (QE), U47.5 (I5)
unnamed: RN20.7 (R6), U39.5 (QF), U47.6 (I6)
unnamed: RN20.8 (R7), U39.6 (QG), U47.7 (I7)
unnamed: RN20.9 (R8), U39.7 (QH), U47.8 (I8)
unnamed: RN21.2 (R1), U40.15 (QA), U48.1 (I1)
unnamed: RN21.3 (R2), U40.1 (QB), U48.2 (I2)
unnamed: RN21.4 (R3), U40.2 (QC), U48.3 (I3)
unnamed: RN21.5 (R4), U40.3 (QD), U48.4 (I4)
unnamed: RN21.6 (R5), U40.4 (QE), U48.5 (I5)
unnamed: RN21.7 (R6), U40.5 (QF), U48.6 (I6)
unnamed: RN21.8 (R7), U40.6 (QG), U48.7 (I7)
unnamed: RN21.9 (R8), U40.7 (QH), U48.8 (I8)
unnamed: RN22.2 (R1), U41.15 (QA), U49.1 (I1)
unnamed: RN22.3 (R2), U41.1 (QB), U49.2 (I2)
unnamed: RN22.4 (R3), U41.2 (QC), U49.3 (I3)
unnamed: RN22.5 (R4), U41.3 (QD), U49.4 (I4)
unnamed: RN22.6 (R5), U41.4 (QE), U49.5 (I5)
unnamed: RN22.7 (R6), U41.5 (QF), U49.6 (I6)
unnamed: RN22.8 (R7), U41.6 (QG), U49.7 (I7)
unnamed: RN22.9 (R8), U41.7 (QH), U49.8 (I8)
unnamed: RN23.2 (R1), U42.15 (QA), U50.1 (I1)
unnamed: RN23.3 (R2), U42.1 (QB), U50.2 (I2)
unnamed: RN23.4 (R3), U42.2 (QC), U50.3 (I3)
unnamed: RN23.5 (R4), U42.3 (QD), U50.4 (I4)
unnamed: RN23.6 (R5), U42.4 (QE), U50.5 (I5)
unnamed: RN23.7 (R6), U42.5 (QF), U50.6 (I6)
unnamed: RN23.8 (R7), U42.6 (QG), U50.7 (I7)
unnamed: RN23.9 (R8), U42.7 (QH), U50.8 (I8)
unnamed: RN24.2 (R1), U43.15 (QA), U51.1 (I1)
unnamed: RN24.3 (R2), U43.1 (QB), U51.2 (I2)
unnamed: RN24.4 (R3), U43.2 (QC), U51.3 (I3)
unnamed: RN24.5 (R4), U43.3 (QD), U51.4 (I4)
unnamed: RN24.6 (R5), U43.4 (QE), U51.5 (I5)
unnamed: RN24.7 (R6), U43.5 (QF), U51.6 (I6)
unnamed: RN24.8 (R7), U43.6 (QG), U51.7 (I7)
unnamed: RN24.9 (R8), U43.7 (QH), U51.8 (I8)
unnamed: U4.9 (QH_2), U5.14 (SER)
unnamed: U5.9 (QH_2), U6.14 (SER)
unnamed: U6.9 (QH_2), U7.14 (SER)
unnamed: U7.9 (QH_2), U8.14 (SER)
unnamed: U8.9 (QH_2), U9.14 (SER)
unnamed: U10.9 (QH_2), U11.14 (SER)
unnamed: U9.9 (QH_2), U10.14 (SER)
unnamed: U11.9 (QH_2), U20.14 (SER)
unnamed: U20.9 (QH_2), U21.14 (SER)
unnamed: U21.9 (QH_2), U22.14 (SER)
unnamed: U22.9 (QH_2), U23.14 (SER)
unnamed: U23.9 (QH_2), U24.14 (SER)
unnamed: U24.9 (QH_2), U25.14 (SER)
unnamed: U25.9 (QH_2), U26.14 (SER)
unnamed: U26.9 (QH_2), U27.14 (SER)
unnamed: U36.9 (QH_2), U37.14 (SER)
unnamed: U37.9 (QH_2), U38.14 (SER)
unnamed: U38.9 (QH_2), U39.14 (SER)
unnamed: U39.9 (QH_2), U40.14 (SER)
unnamed: U40.9 (QH_2), U41.14 (SER)
unnamed: U41.9 (QH_2), U42.14 (SER)
unnamed: U42.9 (QH_2), U43.14 (SER)
ROW 1: U12.18 (O1), U13.18 (O1), U16.18 (O1), U17.18 (O1), U28.18 (O1), U29.18 (O1), U32.18 (O1), U33.18 (O1)
ROW 1 +V: J1.23, J2.23, J5.23, J6.23
ROW 1 GND: J1.21, J2.21, J5.21, J6.21
ROW 2: U12.17 (O2), U13.17 (O2), U16.17 (O2), U17.17 (O2), U28.17 (O2), U29.17 (O2), U32.17 (O2), U33.17 (O2)
ROW 2 +V: J1.27, J2.27, J5.27, J6.27
ROW 2 GND: J1.25, J2.25, J5.25, J6.25
ROW 3: U12.16 (O3), U13.16 (O3), U16.16 (O3), U17.16 (O3), U28.16 (O3), U29.16 (O3), U32.16 (O3), U33.16 (O3)
ROW 3 +V: J1.19, J2.19, J5.19, J6.19
ROW 3 GND: J1.17, J2.17, J5.17, J6.17
ROW 4: U12.15 (O4), U13.15 (O4), U16.15 (O4), U17.15 (O4), U28.15 (O4), U29.15 (O4), U32.15 (O4), U33.15 (O4)
ROW 4 +V: J1.31, J2.31, J5.31, J6.31
ROW 4 GND: J1.29, J2.29, J5.29, J6.29
ROW 5: U12.14 (O5), U13.14 (O5), U16.14 (O5), U17.14 (O5), U28.14 (O5), U29.14 (O5), U32.14 (O5), U33.14 (O5)
ROW 5 +V: J1.15, J2.15, J5.15, J6.15
ROW 5 GND: J1.13, J2.13, J5.13, J6.13
ROW 6: U12.13 (O6), U13.13 (O6), U16.13 (O6), U17.13 (O6), U28.13 (O6), U29.13 (O6), U32.13 (O6), U33.13 (O6)
ROW 6 +V: J1.35, J2.35, J5.35, J6.35
ROW 6 GND: J1.33, J2.33, J5.33, J6.33
ROW 7: U12.12 (O7), U13.12 (O7), U16.12 (O7), U17.12 (O7), U28.12 (O7), U29.12 (O7), U32.12 (O7), U33.12 (O7)
ROW 7 +V: J1.9, J2.9, J5.9, J6.9
ROW 7 GND: J1.5, J2.5, J5.5, J6.5
ROW 8: U12.11 (O8), U13.11 (O8), U16.11 (O8), U17.11 (O8), U28.11 (O8), U29.11 (O8), U32.11 (O8), U33.11 (O8)
ROW 8 +V: J1.43, J2.43, J5.43, J6.43
ROW 8 GND: J1.39, J2.39, J5.39, J6.39
ROW 9: U14.18 (O1), U15.18 (O1), U18.18 (O1), U19.18 (O1), U30.18 (O1), U31.18 (O1), U34.18 (O1), U35.18 (O1)
ROW 9 +V: J3.1, J4.1, J7.1, J8.1
ROW 9 GND: J3.2, J4.2, J7.2, J8.2
ROW 10: U14.17 (O2), U15.17 (O2), U18.17 (O2), U19.17 (O2), U30.17 (O2), U31.17 (O2), U34.17 (O2), U35.17 (O2)
ROW 10 +V: J3.3, J4.3, J7.3, J8.3
ROW 10 GND: J3.4, J4.4, J7.4, J8.4
ROW 11: U14.16 (O3), U15.16 (O3), U18.16 (O3), U19.16 (O3), U30.16 (O3), U31.16 (O3), U34.16 (O3), U35.16 (O3)
ROW 11 +V: J3.5, J4.5, J7.5, J8.5
ROW 11 GND: J3.6, J4.6, J7.6, J8.6
ROW 12: U14.15 (O4), U15.15 (O4), U18.15 (O4), U19.15 (O4), U30.15 (O4), U31.15 (O4), U34.15 (O4), U35.15 (O4)
ROW 12 +V: J3.7, J4.7, J7.7, J8.7
ROW 12 GND: J3.8, J4.8, J7.8, J8.8
ROW 13: U14.14 (O5), U15.14 (O5), U18.14 (O5), U19.14 (O5), U30.14 (O5), U31.14 (O5), U34.14 (O5), U35.14 (O5)
ROW 13 +V: J3.9, J4.9, J7.9, J8.9
ROW 13 GND: J3.10, J4.10, J7.10, J8.10
ROW 14: U14.13 (O6), U15.13 (O6), U18.13 (O6), U19.13 (O6), U30.13 (O6), U31.13 (O6), U34.13 (O6), U35.13 (O6)
ROW 14 +V: J3.11, J4.11, J7.11, J8.11
ROW 14 GND: J3.12, J4.12, J7.12, J8.12
ROW 15: U14.12 (O7), U15.12 (O7), U18.12 (O7), U19.12 (O7), U30.12 (O7), U31.12 (O7), U34.12 (O7), U35.12 (O7)
ROW 15 +V: J3.13, J4.13, J7.13, J8.13
ROW 15 GND: J3.14, J4.14, J7.14, J8.14
ROW 16: U14.11 (O8), U15.11 (O8), U18.11 (O8), U19.11 (O8), U30.11 (O8), U31.11 (O8), U34.11 (O8), U35.11 (O8)
ROW 16 +V: J3.15, J4.15, J7.15, J8.15
ROW 16 GND: J3.16, J4.16, J7.16, J8.16
RTC Module: A1.20, A1.21
Temperature Module: A1.12

Notes on the sheet:
Col "x" connects to col x on board 1, 2, 3, and 4. In other words, columns are synced across boards. Rows are not synced.
BOARD 4 ROWS
BOARD 2 ROWS
BOARD 3 ROWS
B1-4: 1-28, 29-32NC
BOARD 1 ROWS
COLUMNS
