tylerebowers/Luminator-Flipdot-Display/Other/board that doesn't work/luminator.kicad_sch

## KiCad design Other/board that doesn't work/luminator.kicad_sch (2023-12-26, an earlier design)

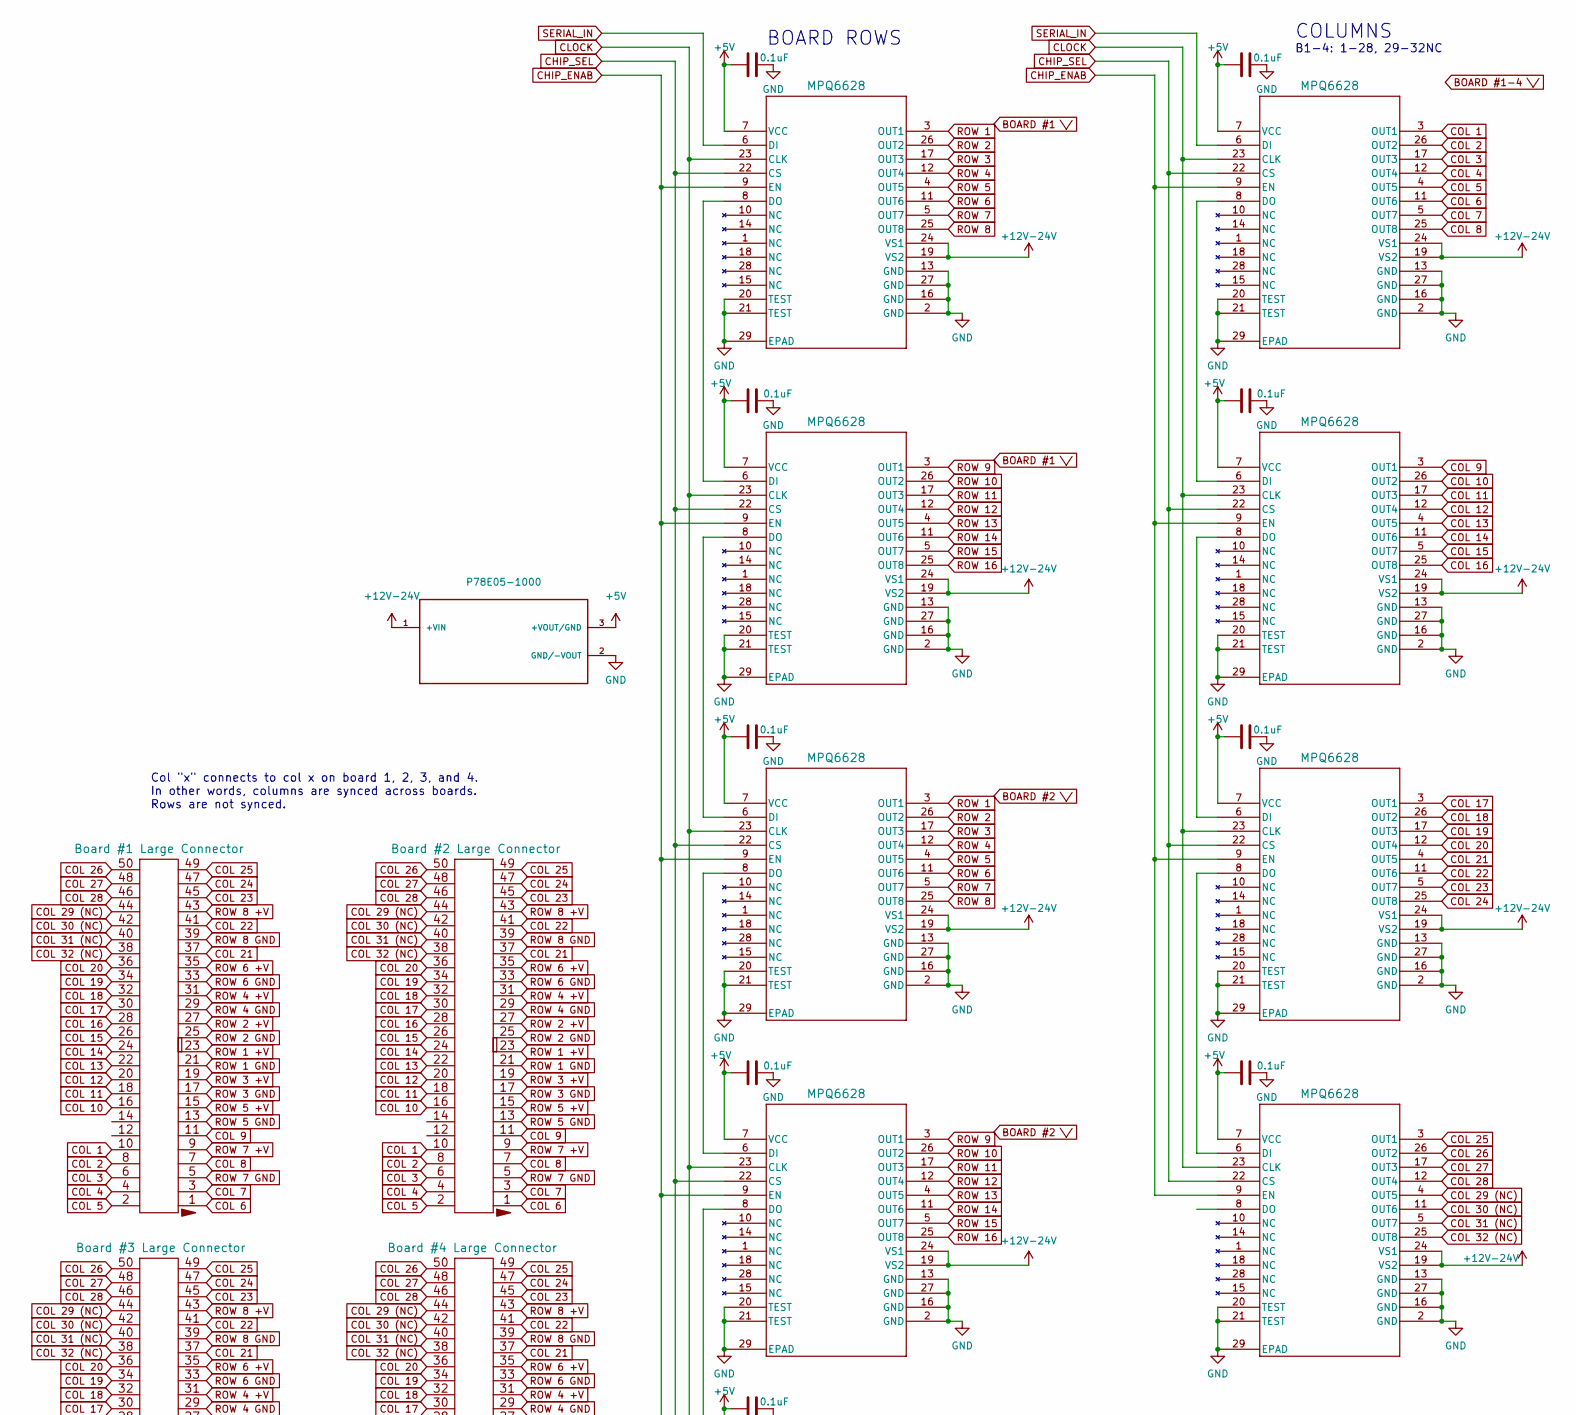
[picture p34: schematic luminator.kicad_sch, part in row 1, column 1]

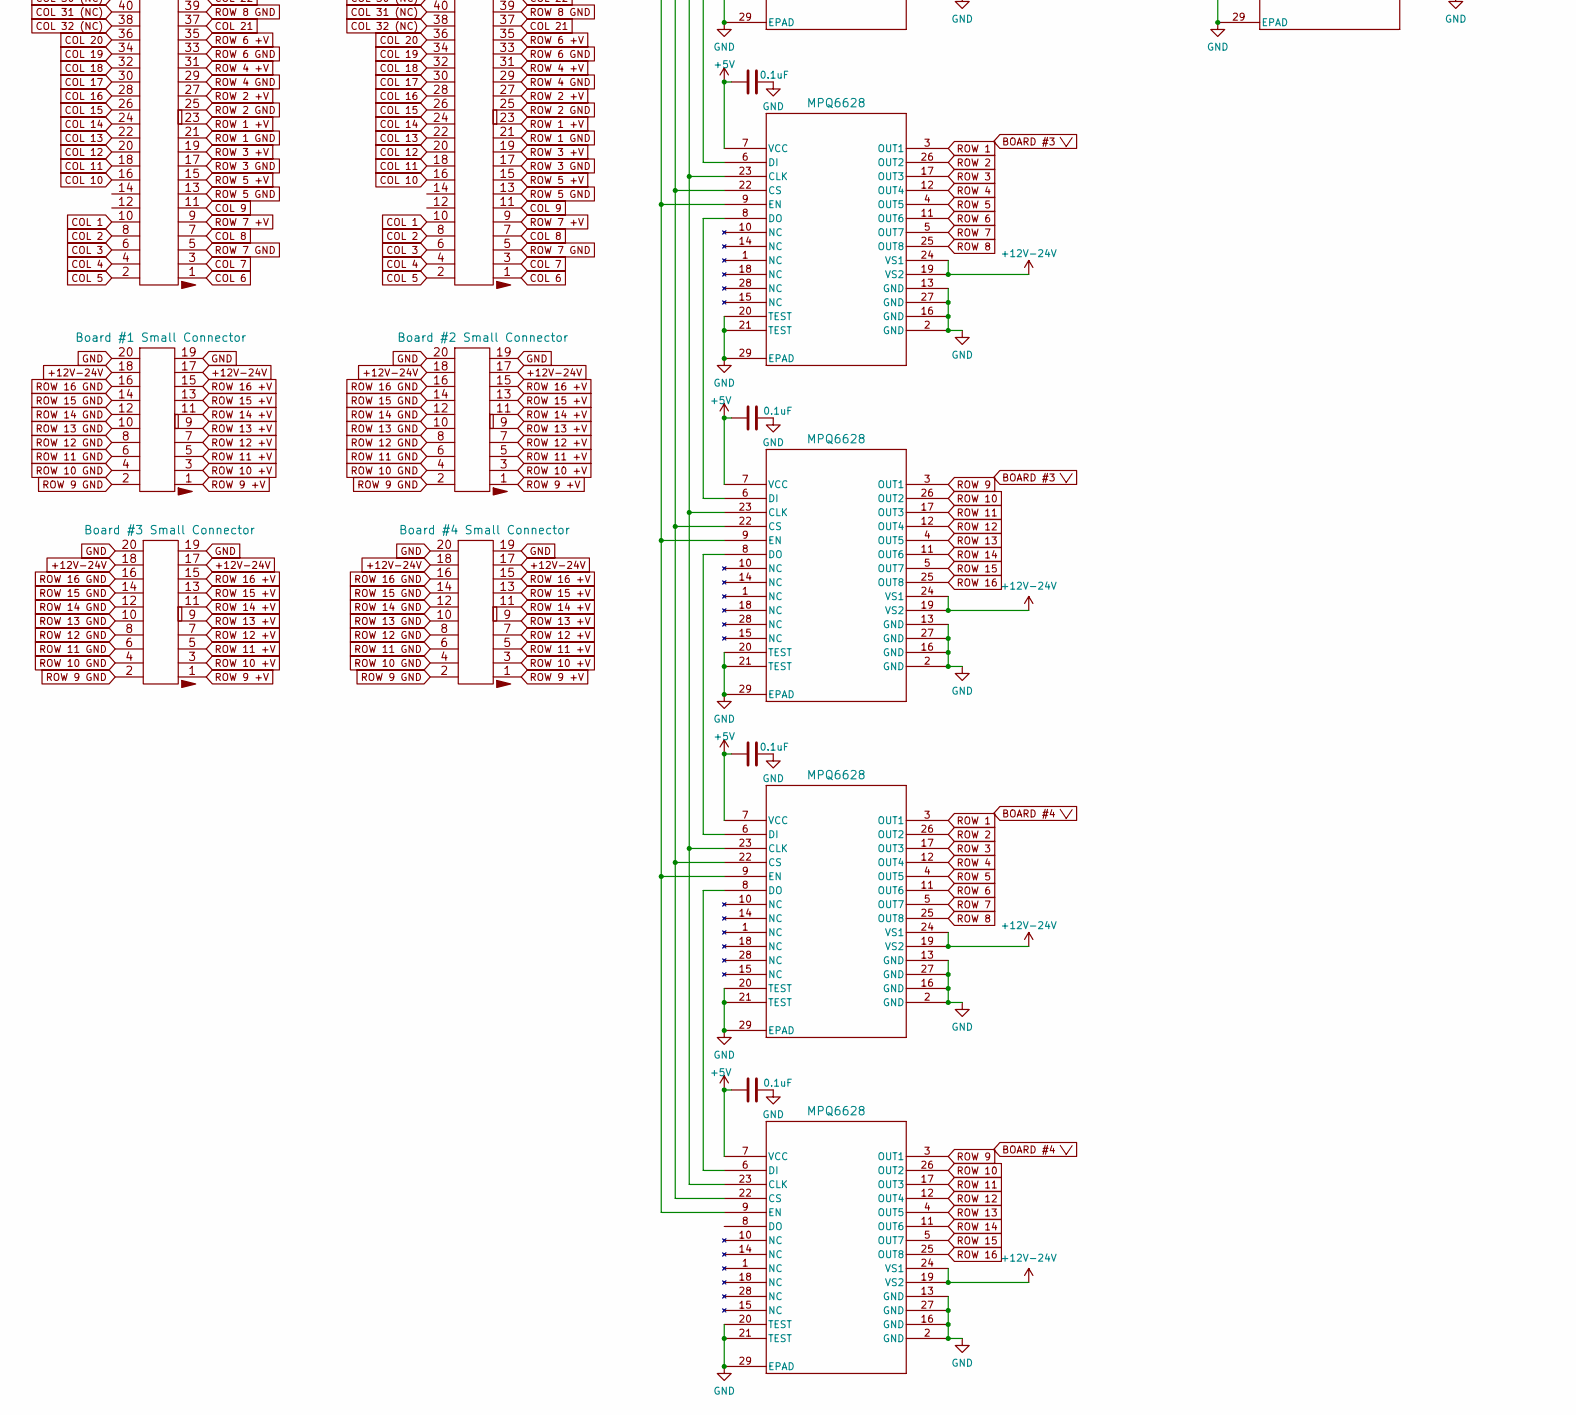
[picture p35: schematic luminator.kicad_sch, part in row 2, column 1]

Parts:
C1, C2, C3, C4, C5, C6, C7, C8, C9, C10, C11, C12: 0.1uF
J1: Board #1 Large Connector; CONN_SBH11-PBPC-D25-ST-BK_SUL
J2: Board #3 Large Connector; CONN_SBH11-PBPC-D25-ST-BK_SUL
J3: Board #1 Small Connector; CONN20_D10-ST-BK_SUL
J4: Board #3 Small Connector; CONN20_D10-ST-BK_SUL
J5: Board #2 Large Connector; CONN_SBH11-PBPC-D25-ST-BK_SUL
J6: Board #4 Large Connector; CONN_SBH11-PBPC-D25-ST-BK_SUL
J7: Board #2 Small Connector; CONN20_D10-ST-BK_SUL
J8: Board #4 Small Connector; CONN20_D10-ST-BK_SUL
PS1: P78E05-1000; CONV_P78E05-1000
U4, U5, U6, U7, U8, U9, U10, U11, U12, U13, U14, U15: MPQ6628; TSSOP-28EP_MPQ6628_MNP

Connections:
+5V: C1.1, C2.1, C3.1, C4.1, C5.1, C6.1, C7.1, C8.1, C9.1, C10.1, C11.1, C12.1, PS1.3 (+VOUT/GND), U4.7 (VCC), U5.7 (VCC), U6.7 (VCC), U7.7 (VCC), U8.7 (VCC), U9.7 (VCC), U10.7 (VCC), U11.7 (VCC), U12.7 (VCC), U13.7 (VCC), U14.7 (VCC), U15.7 (VCC)
+12V-24V: J3.17, J3.18, J4.17, J4.18, J7.17, J7.18, J8.17, J8.18, PS1.1 (+VIN), U4.19 (VS2), U4.24 (VS1), U5.19 (VS2), U5.24 (VS1), U6.19 (VS2), U6.24 (VS1), U7.19 (VS2), U7.24 (VS1), U8.19 (VS2), U8.24 (VS1), U9.19 (VS2), U9.24 (VS1), U10.19 (VS2), U10.24 (VS1), U11.19 (VS2), U11.24 (VS1), U12.19 (VS2), U12.24 (VS1), U13.19 (VS2), U13.24 (VS1), U14.19 (VS2), U14.24 (VS1), U15.19 (VS2), U15.24 (VS1)
CHIP_ENAB: U4.9 (EN), U5.9 (EN), U6.9 (EN), U7.9 (EN), U8.9 (EN), U9.9 (EN), U10.9 (EN), U11.9 (EN), U12.9 (EN), U13.9 (EN), U14.9 (EN), U15.9 (EN)
CHIP_SEL: U4.22 (CS), U5.22 (CS), U6.22 (CS), U7.22 (CS), U8.22 (CS), U9.22 (CS), U10.22 (CS), U11.22 (CS), U12.22 (CS), U13.22 (CS), U14.22 (CS), U15.22 (CS)
CLOCK: U4.23 (CLK), U5.23 (CLK), U6.23 (CLK), U7.23 (CLK), U8.23 (CLK), U9.23 (CLK), U10.23 (CLK), U11.23 (CLK), U12.23 (CLK), U13.23 (CLK), U14.23 (CLK), U15.23 (CLK)
COL 1: J1.10, J2.10, J5.10, J6.10, U12.3 (OUT1)
COL 2: J1.8, J2.8, J5.8, J6.8, U12.26 (OUT2)
COL 3: J1.6, J2.6, J5.6, J6.6, U12.17 (OUT3)
COL 4: J1.4, J2.4, J5.4, J6.4, U12.12 (OUT4)
COL 5: J1.2, J2.2, J5.2, J6.2, U12.4 (OUT5)
COL 6: J1.1, J2.1, J5.1, J6.1, U12.11 (OUT6)
COL 7: J1.3, J2.3, J5.3, J6.3, U12.5 (OUT7)
COL 8: J1.7, J2.7, J5.7, J6.7, U12.25 (OUT8)
COL 9: J1.11, J2.11, J5.11, J6.11, U13.3 (OUT1)
COL 10: J1.16, J2.16, J5.16, J6.16, U13.26 (OUT2)
COL 11: J1.18, J2.18, J5.18, J6.18, U13.17 (OUT3)
COL 12: J1.20, J2.20, J5.20, J6.20, U13.12 (OUT4)
COL 13: J1.22, J2.22, J5.22, J6.22, U13.4 (OUT5)
COL 14: J1.24, J2.24, J5.24, J6.24, U13.11 (OUT6)
COL 15: J1.26, J2.26, J5.26, J6.26, U13.5 (OUT7)
COL 16: J1.28, J2.28, J5.28, J6.28, U13.25 (OUT8)
COL 17: J1.30, J2.30, J5.30, J6.30, U14.3 (OUT1)
COL 18: J1.32, J2.32, J5.32, J6.32, U14.26 (OUT2)
COL 19: J1.34, J2.34, J5.34, J6.34, U14.17 (OUT3)
COL 20: J1.36, J2.36, J5.36, J6.36, U14.12 (OUT4)
COL 21: J1.37, J2.37, J5.37, J6.37, U14.4 (OUT5)
COL 22: J1.41, J2.41, J5.41, J6.41, U14.11 (OUT6)
COL 23: J1.45, J2.45, J5.45, J6.45, U14.5 (OUT7)
COL 24: J1.47, J2.47, J5.47, J6.47, U14.25 (OUT8)
COL 25: J1.49, J2.49, J5.49, J6.49, U15.3 (OUT1)
COL 26: J1.50, J2.50, J5.50, J6.50, U15.26 (OUT2)
COL 27: J1.48, J2.48, J5.48, J6.48, U15.17 (OUT3)
COL 28: J1.46, J2.46, J5.46, J6.46, U15.12 (OUT4)
COL 29 (NC): J1.44, J2.44, J5.44, J6.44, U15.4 (OUT5)
COL 30 (NC): J1.42, J2.42, J5.42, J6.42, U15.11 (OUT6)
COL 31 (NC): J1.40, J2.40, J5.40, J6.40, U15.5 (OUT7)
COL 32 (NC): J1.38, J2.38, J5.38, J6.38, U15.25 (OUT8)
GND: C1.2, C2.2, C3.2, C4.2, C5.2, C6.2, C7.2, C8.2, C9.2, C10.2, C11.2, C12.2, J3.19, J3.20, J4.19, J4.20, J7.19, J7.20, J8.19, J8.20, PS1.2 (GND/-VOUT), U4.2 (GND), U4.13 (GND), U4.16 (GND), U4.20 (TEST), U4.21 (TEST), U4.27 (GND), U4.29 (EPAD), U5.2 (GND), U5.13 (GND), U5.16 (GND), U5.20 (TEST), U5.21 (TEST), U5.27 (GND), U5.29 (EPAD), U6.2 (GND), U6.13 (GND), U6.16 (GND), U6.20 (TEST), U6.21 (TEST), U6.27 (GND), U6.29 (EPAD), U7.2 (GND), U7.13 (GND), U7.16 (GND), U7.20 (TEST), U7.21 (TEST), U7.27 (GND), U7.29 (EPAD), U8.2 (GND), U8.13 (GND), U8.16 (GND), U8.20 (TEST), U8.21 (TEST), U8.27 (GND), U8.29 (EPAD), U9.2 (GND), U9.13 (GND), U9.16 (GND), U9.20 (TEST), U9.21 (TEST), U9.27 (GND), U9.29 (EPAD), U10.2 (GND), U10.13 (GND), U10.16 (GND), U10.20 (TEST), U10.21 (TEST), U10.27 (GND), U10.29 (EPAD), U11.2 (GND), U11.13 (GND), U11.16 (GND), U11.20 (TEST), U11.21 (TEST), U11.27 (GND), U11.29 (EPAD), U12.2 (GND), U12.13 (GND), U12.16 (GND), U12.20 (TEST), U12.21 (TEST), U12.27 (GND), U12.29 (EPAD), U13.2 (GND), U13.13 (GND), U13.16 (GND), U13.20 (TEST), U13.21 (TEST), U13.27 (GND), U13.29 (EPAD), U14.2 (GND), U14.13 (GND), U14.16 (GND), U14.20 (TEST), U14.21 (TEST), U14.27 (GND), U14.29 (EPAD), U15.2 (GND), U15.13 (GND), U15.16 (GND), U15.20 (TEST), U15.21 (TEST), U15.27 (GND), U15.29 (EPAD)
unnamed: U4.8 (DO), U5.6 (DI)
unnamed: U5.8 (DO), U6.6 (DI)
unnamed: U6.8 (DO), U7.6 (DI)
unnamed: U7.8 (DO), U8.6 (DI)
unnamed: U8.8 (DO), U9.6 (DI)
unnamed: U9.8 (DO), U10.6 (DI)
unnamed: U10.8 (DO), U11.6 (DI)
unnamed: U12.8 (DO), U13.6 (DI)
unnamed: U13.8 (DO), U14.6 (DI)
unnamed: U14.8 (DO), U15.6 (DI)
ROW 1: U4.3 (OUT1), U6.3 (OUT1), U8.3 (OUT1), U10.3 (OUT1)
ROW 1 +V: J1.23, J2.23, J5.23, J6.23
ROW 1 GND: J1.21, J2.21, J5.21, J6.21
ROW 2: U4.26 (OUT2), U6.26 (OUT2), U8.26 (OUT2), U10.26 (OUT2)
ROW 2 +V: J1.27, J2.27, J5.27, J6.27
ROW 2 GND: J1.25, J2.25, J5.25, J6.25
ROW 3: U4.17 (OUT3), U6.17 (OUT3), U8.17 (OUT3), U10.17 (OUT3)
ROW 3 +V: J1.19, J2.19, J5.19, J6.19
ROW 3 GND: J1.17, J2.17, J5.17, J6.17
ROW 4: U4.12 (OUT4), U6.12 (OUT4), U8.12 (OUT4), U10.12 (OUT4)
ROW 4 +V: J1.31, J2.31, J5.31, J6.31
ROW 4 GND: J1.29, J2.29, J5.29, J6.29
ROW 5: U4.4 (OUT5), U6.4 (OUT5), U8.4 (OUT5), U10.4 (OUT5)
ROW 5 +V: J1.15, J2.15, J5.15, J6.15
ROW 5 GND: J1.13, J2.13, J5.13, J6.13
ROW 6: U4.11 (OUT6), U6.11 (OUT6), U8.11 (OUT6), U10.11 (OUT6)
ROW 6 +V: J1.35, J2.35, J5.35, J6.35
ROW 6 GND: J1.33, J2.33, J5.33, J6.33
ROW 7: U4.5 (OUT7), U6.5 (OUT7), U8.5 (OUT7), U10.5 (OUT7)
ROW 7 +V: J1.9, J2.9, J5.9, J6.9
ROW 7 GND: J1.5, J2.5, J5.5, J6.5
ROW 8: U4.25 (OUT8), U6.25 (OUT8), U8.25 (OUT8), U10.25 (OUT8)
ROW 8 +V: J1.43, J2.43, J5.43, J6.43
ROW 8 GND: J1.39, J2.39, J5.39, J6.39
ROW 9: U5.3 (OUT1), U7.3 (OUT1), U9.3 (OUT1), U11.3 (OUT1)
ROW 9 +V: J3.1, J4.1, J7.1, J8.1
ROW 9 GND: J3.2, J4.2, J7.2, J8.2
ROW 10: U5.26 (OUT2), U7.26 (OUT2), U9.26 (OUT2), U11.26 (OUT2)
ROW 10 +V: J3.3, J4.3, J7.3, J8.3
ROW 10 GND: J3.4, J4.4, J7.4, J8.4
ROW 11: U5.17 (OUT3), U7.17 (OUT3), U9.17 (OUT3), U11.17 (OUT3)
ROW 11 +V: J3.5, J4.5, J7.5, J8.5
ROW 11 GND: J3.6, J4.6, J7.6, J8.6
ROW 12: U5.12 (OUT4), U7.12 (OUT4), U9.12 (OUT4), U11.12 (OUT4)
ROW 12 +V: J3.7, J4.7, J7.7, J8.7
ROW 12 GND: J3.8, J4.8, J7.8, J8.8
ROW 13: U5.4 (OUT5), U7.4 (OUT5), U9.4 (OUT5), U11.4 (OUT5)
ROW 13 +V: J3.9, J4.9, J7.9, J8.9
ROW 13 GND: J3.10, J4.10, J7.10, J8.10
ROW 14: U5.11 (OUT6), U7.11 (OUT6), U9.11 (OUT6), U11.11 (OUT6)
ROW 14 +V: J3.11, J4.11, J7.11, J8.11
ROW 14 GND: J3.12, J4.12, J7.12, J8.12
ROW 15: U5.5 (OUT7), U7.5 (OUT7), U9.5 (OUT7), U11.5 (OUT7)
ROW 15 +V: J3.13, J4.13, J7.13, J8.13
ROW 15 GND: J3.14, J4.14, J7.14, J8.14
ROW 16: U5.25 (OUT8), U7.25 (OUT8), U9.25 (OUT8), U11.25 (OUT8)
ROW 16 +V: J3.15, J4.15, J7.15, J8.15
ROW 16 GND: J3.16, J4.16, J7.16, J8.16
SERIAL_IN: U4.6 (DI), U12.6 (DI)

Notes on the sheet:
Col "x" connects to col x on board 1, 2, 3, and 4. In other words, columns are synced across boards. Rows are not synced.
B1-4: 1-28, 29-32NC
BOARD ROWS
COLUMNS
