tylerebowers/Luminator-Flipdot-Display/Software/rpi/main.py

from datetime import datetime
from time import sleep
import threading
import requests
import serial
from library import *


numCols = 112
numRows = 16
city = "West Lafayette"
openWeatherMapAPIKey = "asd asd asd"
openWeatherMapBaseURL = "https://api.openweathermap.org/data/2.5/weather?"
openWeatherMapURL = openWeatherMapBaseURL + "appid=" + openWeatherMapAPIKey + "&q=" + city + "&units=metric"


class flipdots:
    serial = None
    serialPort = "/dev/ttyUSB0"
    baudRate = 115200

    @staticmethod
    def connect():
        try:
            flipdots.serial = serial.Serial(flipdots.serialPort, flipdots.baudRate)
            print("Connected to serial port: " + flipdots.serialPort)
        except:
            print("Failed to connect to serial port: " + flipdots.serialPort)
            flipdots.serial = None


    @staticmethod
    def send(string):
        print(string, end='')
        if flipdots.serial is None or not flipdots.serial.is_open:
            flipdots.connect()
        if flipdots.serial is not None and flipdots.serial.is_open:
            flipdots.serial.write(string.encode('ascii', 'ignore'))
            while flipdots.serial.readline()[0:5] != b'ready':
                sleep(0.5)

    @staticmethod
    def allOff():
        flipdots.send("allOff\n")

    @staticmethod
    def allOn():
        flipdots.send("allOn\n")

    @staticmethod
    def invert():
        flipdots.send("invert\n")


class display:
    interrupt = False

    @staticmethod
    def compileTextArray(string, mode, min = 0):
        tempArray = []
        if mode == "time14":
            for l in string:
                tempArray.append("0")
                for c in time14[l]:
                    tempArray.append(str(c))
            tempArray.append("0")
        if mode == "ascii7":
            for l in string:
                tempArray.append("0")
                for c in ascii7[l]:
                    tempArray.append(str(c))
            tempArray.append("0")
        while len(tempArray) < min:
            tempArray.append("0")
        return tempArray


    @staticmethod
    def timeDayWeather():
        shownMinute = -1
        shownDay = -1
        weatherUpdatedMinute = -30
        while True:
            now = datetime.now()
            if display.interrupt:
                break

            # get time and show in large font
            if now.minute != shownMinute:
                current_time = now.strftime("%-I:%M%p").lower()[0:-1]
                tempArray = display.compileTextArray(current_time, "time14", 54)
                timeCommand = f"({'{' + ','.join(tempArray) + '}'},{len(tempArray)},14,0,1,20)\n"
                flipdots.send(timeCommand)
                # update the current minute that is shown
                shownMinute = now.minute

            # get date and show in small font top right
            if now.day != shownDay:
                line1 = now.strftime("%B !!")
                line1 = line1.replace('!!', str(now.day) + {1:'st',2:'nd',3:'rd'}.get(now.day%20, 'th'))
                tempArray = display.compileTextArray(line1, "ascii7", 57)
                dateCommand = f"({'{' + ','.join(tempArray) + '}'},{len(tempArray)},7,55,0,50)\n"
                flipdots.send(dateCommand)
                # update the current day that is shown
                shownDay = now.day

            # get weather and show in small font bottom right
            if abs(now.minute - weatherUpdatedMinute) > 15:
                response = requests.get(openWeatherMapURL)
                if response.ok:
                    response = response.json()
                    fahrenheit_temperature = (response["main"]["temp"] * 1.8) + 32
                    condition = response["weather"][0]["main"]
                    text = f"{fahrenheit_temperature:.0f}F {condition}"
                else:
                    text = "API call error"
                tempArray = display.compileTextArray(text, "ascii7", 57)
                dateCommand = f"({'{' + ','.join(tempArray) + '}'},{len(tempArray)},7,55,8,50)\n"
                flipdots.send(dateCommand)
                weatherUpdatedMinute = shownMinute

            sleep(5)

    @staticmethod
    def weatherBig():  # weather
        weatherUpdatedMinute = -30
        while True:
            now = datetime.now()
            if display.interrupt:
                break
            if abs(now.minute - weatherUpdatedMinute) > 30:  # get weather
                newDisplay = []
                response = requests.get(openWeatherMapURL)
                if response.ok:
                    response = response.json()
                    celcius_temperature = response["main"]["temp"]
                    fahrenheit_temperature = (celcius_temperature * 1.8) + 32
                    text = f"{celcius_temperature:.0f}C ({fahrenheit_temperature:.0f}F)"
                else:
                    text = "API call error"
                for l in text:
                    newDisplay.append("0")
                    for c in ascii7[l]:
                        newDisplay.append(str(c))
                newDisplay.append("0")
                weatherCommand = f"({'{' + ','.join(newDisplay) + '}'},{len(newDisplay)},7,0,8,50)\n"
                flipdots.send(weatherCommand)
                weatherUpdatedMinute = now.minute


    @staticmethod
    def stocks():  # stocks
        print("stocks")

    @staticmethod
    def stockBig(ticker):  # stock
        print("stockBig")

    @staticmethod
    def news():  # news
        print("news")

    class tests:
        @staticmethod
        def time():  # test
            separator = "({65535},1,16,56,0,50)\n"
            flipdots.send(separator)
            for h in range(0, 24):
                for m in [0,1,23,34,56,57,58,59]:
                    dt = datetime.strptime(f"{h:02d}:{m:02d}:00", "%H:%M:%S")
                    current_time = dt.strftime("%-I:%M%p").lower()[0:-1]
                    tempArray = display.compileTextArray(current_time, "time14", 56)
                    timeCommand = f"({'{' + ','.join(tempArray) + '}'},{len(tempArray)},14,0,1,20)\n"
                    flipdots.send(timeCommand)
                    sleep(0.5)

        @staticmethod
        def purdue():
            flipdots.send(f"{'{' + ','.join([str(c) for c in purdue]) + '}'}")
            sleep(10)

        @staticmethod
        def alphabet():
            for i in range(0, 3):
                temp = ascii7.copy()
                while len(temp) > 0:
                    line1 = []
                    line2 = []
                    for k in list(temp.keys()):
                        if len(line1) < 104:
                            for c in temp[k]:
                                line1.append(str(c))
                            line1.append("0")
                            del temp[k]
                        else: break
                    for k in list(temp.keys()):
                        if len(line2) < 104:
                            for c in temp[k]:
                                line2.append(str(c))
                            line2.append("0")
                            del temp[k]
                        else: break
                    c1 = f"({'{' + ','.join(line1) + '}'},112,7,0,0,20)\n"
                    flipdots.send(c1)
                    c2 = f"({'{' + ','.join(line2) + '}'},112,7,0,8,20)\n"
                    flipdots.send(c2)
                    sleep(10)


def displayLoop():
    display.tests.purdue()
    flipdots.allOff()
    display.timeDayWeather()
    #display.tests.alphabet()
    #display.tests.time()


def main():
    # start webApp and wait for interrupts
    return

if __name__ == "__main__":
    flipdots.connect()
    flipdots.allOff()
    threading.Thread(target=displayLoop).start()
    main()
