tylerebowers/Luminator-Flipdot-Display/Software/rpi/library.py

"""
This file stores ascii characters for use in the display.
variable names are ascii_ where _ is the height for the characters
"""


ascii7 = {	            #-32
    " ":  [0,0],
    "!":  [95],
    "\"": [3,0,3],
    "#":  [20,62,20,62,20],
    "$":  [46,42,127,42,58],
    "%":  [2,101,62,83,32],
    "&":  [54,73,81,34,80],
    "\'": [3],
    "(":  [62,65],
    ")":  [65,62],
    "*":  [20,8,20],
    "+":  [8,28,8],
    ",":  [96],
    "-":  [8,8,8],
    ".":  [64],
    "/":  [96,28,3],
    "0":  [62,65,65,62],
    "1":  [66,127,64],
    "2":  [98,81,73,70],
    "3":  [73,73,54],
    "4":  [15,8,127,8],
    "5":  [79,73,73,49],
    "6":  [62,73,73,48],
    "7":  [1,97,25,7],
    "8":  [54,73,73,54],
    "9":  [6,73,73,62],
    ":":  [36],
    ";":  [64,36],
    "<":  [8,20,34],
    "=":  [20,20,20],
    ">":  [34,20,8],
    "?":  [2,81,9,6],
    "@":  [62,65,93,85,14],
    "A":  [126,9,9,126],
    "B":  [127,73,73,62],
    "C":  [62,65,65,34],
    "D":  [127,65,65,62],
    "E":  [127,73,65],
    "F":  [127,9,9],
    "G":  [62,65,73,58],
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
}

ascii7_2 = [
    [ 0, 0, 0, 0],            #
    [ 6, 95, 6, 0],           # !
    [7, 3, 0, 7, 3],            # "
    [36, 126, 36, 126, 36],     # #
    [36, 43, 106, 18, 0],       # $
    [99, 19, 8, 100, 99],       # %
    [54, 73, 86, 32, 80],       # &
    [ 7, 3, 0, 0],            # '
    [ 62, 65, 0, 0],          # (
    [ 65, 62, 0, 0],          # )
    [8, 62, 28, 62, 8],         # *
    [8, 8, 62, 8, 8],           # +
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
