tylerebowers/Luminator-Flipdot-Display/Software/rpi/test.py

from datetime import datetime
"""
toConvert = [
    [0x00, 0x00, 0x00],  #
    [0x22, 0x20, 0x20],  # !
    [0x55, 0x00, 0x00],  # "
    [0x57, 0x57, 0x50],  ##
    [0x23, 0x63, 0x62],  # $
    [0x41, 0x24, 0x10],  # %
    [0x25, 0x35, 0x70],  # &
    [0x64, 0x00, 0x00],  # '
    [0x24, 0x44, 0x20],  # (
    [0x42, 0x22, 0x40],  # )
    [0x52, 0x72, 0x50],  # *
    [0x02, 0x72, 0x00],  # +
    [0x00, 0x00, 0x64],  # ,
    [0x00, 0x70, 0x00],  # -
    [0x00, 0x00, 0x20],  # .
    [0x11, 0x24, 0x40],  # /
    [0x35, 0x55, 0x60],  # 0
    [0x26, 0x22, 0x70],  # 1
    [0x61, 0x24, 0x70],  # 2
    [0x61, 0x21, 0x60],  # 3
    [0x15, 0x71, 0x10],  # 4
    [0x74, 0x61, 0x60],  # 5
    [0x24, 0x65, 0x20],  # 6
    [0x71, 0x32, 0x20],  # 7
    [0x25, 0x25, 0x20],  # 8
    [0x25, 0x31, 0x20],  # 9
    [0x00, 0x20, 0x20],  #:
    [0x00, 0x20, 0x64],  # ;
    [0x12, 0x42, 0x10],  # <
    [0x00, 0x70, 0x70],  # =
    [0x42, 0x12, 0x40],  # >
    [0x61, 0x20, 0x20],  # ?
    [0x75, 0x54, 0x70],  # @
    [0x25, 0x75, 0x50],  # A
    [0x65, 0x65, 0x60],  # B
    [0x34, 0x44, 0x30],  # C
    [0x65, 0x55, 0x60],  # D
    [0x74, 0x64, 0x70],  # E
    [0x74, 0x64, 0x40],  # F
    [0x34, 0x55, 0x30],  # G
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
]


for l in toConvert:
    s = "".join(format(i, '08b') for i in l)
    arr = []
    for i in range(0, 4):
        b = ""
        for j in range(0, 6):
            b += s[(j*4)+i]

        arr.append(int(b[::-1], 2))
    print(arr)

    #f bin(i[0]) bin(i[1]), bin(i[2]), bin(i[3]), bin(i[4]), bin(i[5])

"""
"""
now = datetime.now()
print(now.strftime("%I:%M%p").lower()[0:-1])
current_date = now.strftime("%A, %B !!")
current_date = current_date.replace('!!', str(now.day) + {1:'st',2:'nd',3:'rd'}.get(now.day%20, 'th'))
print(current_date)
"""

import requests
city = "West Lafayette"
openWeatherMapAPIKey = "your api key"
openWeatherMapBaseURL = "https://api.openweathermap.org/data/2.5/weather?"
openWeatherMapURL = openWeatherMapBaseURL + "appid=" + openWeatherMapAPIKey + "&q=" + city + "&units=imperial"
response = requests.get(openWeatherMapURL)
print(response.json())
if response.ok:
    response = response.json()
    current_temperature = response["main"]["temp"]
    print(current_temperature)

"""
#print(datetime.now().strftime("%#I:%M%p").lower()[0:-1])
from simulator import simulator
sim = simulator()
sim.print()
sim.readString("{0,0,11838,10760,14856,62,14336,8254,14378,42,14336,2110,12320,32,14336,2110,12320,32,14336,8254,63522,62,0,0,0,3584,2048,15934,32,15934,8736,15934,0,574,14370,10302,0,62,26,46,0,62,32,32,0,62,34,28,0,0,0,0,0,0,0,0,0,0,0,24830,24830,24774,24774,24774,29126,16262,7942,0,1584,1584,0,8184,16380,28686,24582,24582,24582,24582,28686,16380,8184,0,0,8184,16380,28686,24582,24582,24582,24582,28686,16380,8184,0,63488,10240,14336,0,14336,2048,14336,2048,14336,0,0,0,0,0,0,0,0,0}\n")
sim.print()
sim.allOff()
sim.readString("({7,3,1,1,1}, 5, 3, 2, 6, 1)\n")
sim.print()
sim.allOff()
sim.readString("(7,3,1)\n")
sim.print()
sim.allOff()
"""
